TeTeHacko/chytra-budka/firmware/hw/chytra-budka.kicad_sch

## KiCad design firmware/hw/chytra-budka.kicad_sch (2026-08-27)

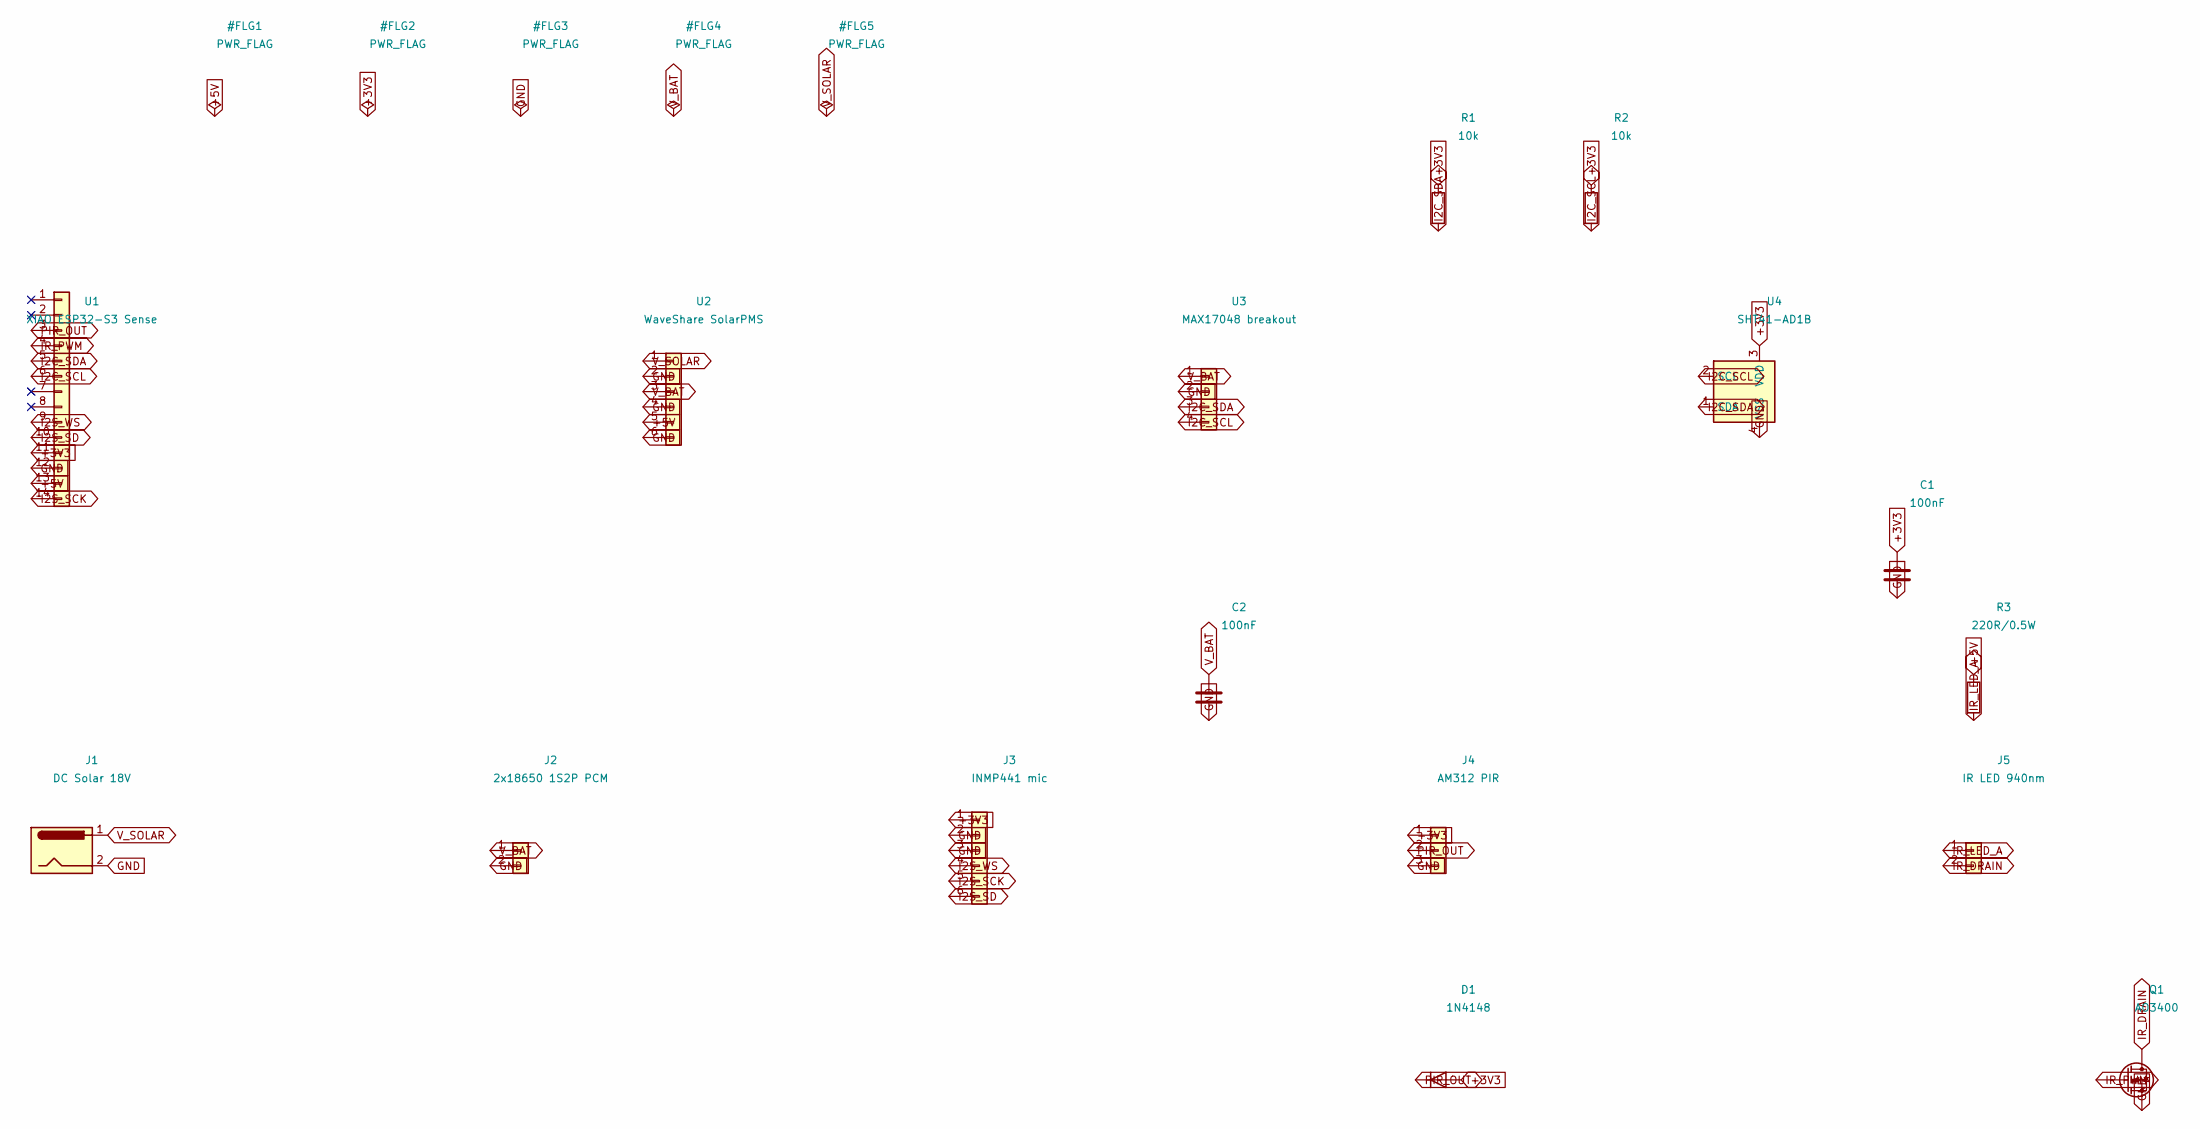
[picture p6: schematic chytra-budka.kicad_sch]

Parts:
C1, C2: 100nF
D1: 1N4148
J1: DC Solar 18V
J2: 2x18650 1S2P PCM
J3: INMP441 mic
J4: AM312 PIR
J5: IR LED 940nm
Q1: AO3400
R1, R2: 10k
R3: 220R/0.5W
U1: XIAO ESP32-S3 Sense
U2: WaveShare SolarPMS
U3: MAX17048 breakout
U4: SHT41-AD1B

Connections:
+3V3: C1.1, D1.2 (A), J3.1, J4.1, R1.1, R2.1, U1.11, U4.3 (VDD)
+5V: R3.1, U1.13, U2.5
GND: C1.2, C2.2, J1.2, J2.2, J3.2, J3.3, J4.3, Q1.S, U1.12, U2.2, U2.4, U2.6, U3.2, U4.4 (VSS)
I2C_SCL: R2.2, U1.6, U3.4, U4.2 (SCL)
I2C_SDA: R1.2, U1.5, U3.3, U4.1 (SDA)
I2S_SCK: J3.5, U1.14
I2S_SD: J3.6, U1.10
I2S_WS: J3.4, U1.9
IR_DRAIN: J5.2, Q1.D
IR_LED_A: J5.1, R3.2
IR_PWM: Q1.G, U1.4
PIR_OUT: D1.1 (K), J4.2, U1.3
V_BAT: C2.1, J2.1, U2.3, U3.1
V_SOLAR: J1.1, U2.1
