TeTeHacko/chytra-budka/firmware/main/http_server.c

/* http_server.c — local HTTP endpoints. See http_server.h. */
#include "http_server.h"

#include "app_config.h"
#include "ble.h"
#include "ble_store.h"
#include "uart_servo.h"

#include <stdio.h>
#include <string.h>

#include <ctype.h>
#include <dirent.h>
#include <errno.h>
#include <fcntl.h>
#include <inttypes.h>
#include <math.h>
#include <stdatomic.h>
#include <stdlib.h>
#include <strings.h>
#include <sys/stat.h>
#include <unistd.h>

#include "app_main_exports.h"
#include "audio.h"
#include "battery.h"
#include "camera.h"
#include "exif_read.h"
#include "config.h"
#include "glitchtip.h"
#include "secrets.h"
#include "secret_helpers.h"
#include "auth_store.h"
#include "tls_enroll.h"
#include "tls_store.h"
#include "wifi_mgr.h"
#include "wifi_store.h"
#include "i18n.h"
#include "sd_layout.h"
#include "ota.h"
#include "esp_system.h"
#include "driver/gpio.h"
#include "device_id.h"
#include "diag.h"
#include "esp_app_desc.h"
#include "esp_heap_caps.h"
#include "freertos/FreeRTOS.h"
#include "freertos/semphr.h"
#include "freertos/task.h"
#include "cb_time.h"
#include "esp_http_server.h"
#include "esp_https_server.h"
#include "esp_log.h"
#include "esp_mac.h"
#include "esp_timer.h"
#include "esp_wifi.h"
#include "mbedtls/base64.h"
#include "i2c_bb.h"
#include "i2c_bus.h"
#include "mqtt.h"
#include "pir.h"
#include "reed.h"
#include "soil.h"
#include "sonar.h"
#include "oled.h"
#include "sd_storage.h"
#include "sensors.h"
#include "text_util.h"
#include "wifi_mgr.h"

static const char *TAG = "http";

/* BLE web-UI helpers shared by root_get (a summary table of connected meters)
 * and the /ble management page, both defined later in this file. */
#define BLE_VIEW_MAX 24
/* Bytes of a JPEG to peek when reading EXIF: the APP1 segment jpeg_stamp.c
 * writes sits right after SOI and is ≤ ~1.1 KB, so 2 KB is ample headroom and
 * avoids copying/parsing the whole (UXGA) frame. */
#define EXIF_PEEK_BYTES 2048

/* Scratch buffer for non-DMA per-request work (EXIF header peeks, SD file
 * reads). Prefer PSRAM so we don't add pressure to the scarce internal DRAM
 * that the BT controller + HW-AES (TLS handshakes) compete for — small plain
 * malloc()s land in internal DRAM (SPIRAM_MALLOC_ALWAYSINTERNAL=4096). Falls
 * back to internal if PSRAM is full. Free with the normal free(). */
static void *scratch_alloc(size_t n) {
    void *p = heap_caps_malloc(n, MALLOC_CAP_SPIRAM);
    return p ? p : malloc(n);
}

static void ble_values_html(const ble_dev_view_t *v, char *out, size_t cap);
static void scan_html_escape(const char *s, char *out, size_t cap);
static void scan_url_decode(const char *s, char *out, size_t cap);

static httpd_handle_t s_server       = NULL;
static httpd_handle_t s_redirect_srv = NULL;
/* True after http_server_start() came up over TLS. HSTS + the Basic
 * auth gate are conditional on this — when the board is in the
 * pre-enrollment HTTP fallback (no cert yet), we don't ship HSTS (it
 * would lock the browser into a non-existent HTTPS) and we don't ask
 * for Basic credentials (the wire is plaintext, so collecting them
 * would be worse than letting LAN users in unauthenticated). */
static bool           s_https_active = false;
/* Cert+key blob outlives the httpd config struct because esp_https_server
 * copies the bytes into its own arena at start (see https_server.c). We
 * still keep the blob alive for the lifetime of the server so a future
 * reload path can re-use it. NULL when running plain HTTP. */
static tls_store_blob_t *s_tls_blob  = NULL;

/* True when HTTP_BASIC_USER/PASS in secrets.h aren't placeholders. The
 * gate also requires s_https_active — basic creds over plaintext is
 * worse than no gate, since the password is recoverable by anybody on
 * the LAN.
 *
 * TODO(fail-closed): when HTTPS is active and placeholders are still
 * in secrets.h, log a loud ESP_LOGW at startup (or refuse to register
 * sensitive handlers). Today a default-config production build serves
 * /mic.wav etc. unauthenticated over HTTPS, which contradicts the
 * "paranoid" deployment posture. Tracked in HTTPS.md follow-ups. */
static bool basic_auth_enabled(void) {
    if (!s_https_active) return false;
    /* Effective creds = operator-set NVS override (via /config or cmd/auth)
     * else the compile-time secrets.h default. */
    char user[AUTH_STORE_USER_CAP], pass[AUTH_STORE_PASS_CAP];
    auth_store_get_effective(user, sizeof(user), pass, sizeof(pass));
    return !secret_is_placeholder(user) && !secret_is_placeholder(pass);
}

/* Set Strict-Transport-Security on HTTPS responses. max-age=15552000 =
 * 180 days; includeSubDomains is safe because *.lan / *.lan aren't
 * also served plain HTTP outside the budka fleet. Skip on plain HTTP
 * (pre-enrollment) so a browser doesn't pin to a non-existent HTTPS
 * endpoint. Idempotent — handlers can call this in addition to
 * basic_auth_gate; the order doesn't matter. */
static void apply_hsts(httpd_req_t *req) {
    if (!s_https_active) return;
    httpd_resp_set_hdr(req, "Strict-Transport-Security",
                       "max-age=15552000; includeSubDomains");
}

/* Check HTTP Basic auth on the incoming request. Returns:
 *   ESP_OK   — gate disabled OR credentials valid
 *   ESP_FAIL — 401 sent; caller must return ESP_OK (NOT ESP_FAIL) so
 *              the httpd loop doesn't log a spurious error
 * Constant-time strcmp not used — the credential is short, the LAN
 * threat model isn't a timing-attack side-channel; if that changes,
 * swap for a CRYPTO_memcmp. */
static esp_err_t basic_auth_gate(httpd_req_t *req) {
    if (!basic_auth_enabled()) return ESP_OK;

    char hdr[256];
    if (httpd_req_get_hdr_value_str(req, "Authorization", hdr, sizeof(hdr)) != ESP_OK) {
        goto deny;
    }
    /* Expect "Basic <base64>" — anything else (Bearer …, Digest …)
     * gets refused with WWW-Authenticate so the client retries with
     * Basic. Case-insensitive scheme per RFC 7235 §2.1. */
    const char *p = hdr;
    if (strncasecmp(p, "Basic ", 6) != 0) goto deny;
    p += 6;
    while (*p == ' ') p++;

    /* Decode base64 → "USER:PASS". 96 bytes covers a 64-char user +
     * 64-char pass + ':' + slack. Anything longer gets rejected. */
    unsigned char dec[96];
    size_t dec_len = 0;
    if (mbedtls_base64_decode(dec, sizeof(dec) - 1, &dec_len,
                              (const unsigned char *)p, strlen(p)) != 0) {
        goto deny;
    }
    dec[dec_len] = 0;
    char *colon = strchr((char *)dec, ':');
    if (!colon) goto deny;
    *colon = 0;
    const char *user = (const char *)dec;
    const char *pass = colon + 1;

    char user_exp[AUTH_STORE_USER_CAP], pass_exp[AUTH_STORE_PASS_CAP];
    auth_store_get_effective(user_exp, sizeof(user_exp), pass_exp, sizeof(pass_exp));
    if (strcmp(user, user_exp) == 0 && strcmp(pass, pass_exp) == 0) {
        return ESP_OK;
    }

deny:
    httpd_resp_set_status(req, "401 Unauthorized");
    /* Realm string just labels the credential prompt in the browser
     * dialog — "chytra-budka" is enough to disambiguate from any other
     * site the LAN user has bookmarks for. */
    httpd_resp_set_hdr(req, "WWW-Authenticate",
                       "Basic realm=\"chytra-budka\", charset=\"UTF-8\"");
    apply_hsts(req);
    httpd_resp_send(req, "auth required\n", HTTPD_RESP_USE_STRLEN);
    return ESP_FAIL;
}

/* One-liner used at the top of sensitive handlers: enforce the gate
 * and apply HSTS in one go. Returns the value the caller should return
 * (ESP_OK to short-circuit on a 401, since the httpd loop interprets
 * ESP_FAIL as "handler failed, drop the socket"). */
#define HTTP_AUTH_OR_RETURN(req) do {                       \
    if (basic_auth_gate((req)) != ESP_OK) return ESP_OK;    \
    apply_hsts((req));                                      \
} while (0)

static void format_mac(char *out, size_t out_sz) {
    uint8_t mac[6] = {0};
    if (esp_read_mac(mac, ESP_MAC_WIFI_STA) != ESP_OK) {
        snprintf(out, out_sz, "??:??:??:??:??:??");
        return;
    }
    snprintf(out, out_sz, "%02x:%02x:%02x:%02x:%02x:%02x", mac[0], mac[1], mac[2], mac[3], mac[4],
             mac[5]);
}

/* Uptime in operator-readable form: "3d 4h 12m", collapsing leading zero
 * units down to "4h 12m" / "12m 5s" / "45s" so a fresh boot reads sanely too.
 * (MQTT/EXIF keep raw seconds for machine parsing; this is for the web UI.) */
static void fmt_uptime(char *out, size_t cap, int64_t secs) {
    if (secs < 0) secs = 0;
    int d = (int)(secs / 86400);
    int h = (int)((secs % 86400) / 3600);
    int m = (int)((secs % 3600) / 60);
    int s = (int)(secs % 60);
    if (d)      snprintf(out, cap, "%dd %dh %dm", d, h, m);
    else if (h) snprintf(out, cap, "%dh %dm", h, m);
    else if (m) snprintf(out, cap, "%dm %ds", m, s);
    else        snprintf(out, cap, "%ds", s);
}

/* Status-row glyphs (shared by the merged Status table): green tick when a
 * subsystem is ready, amber em-dash otherwise. */
#define ST_TICK "&#10003;"
#define ST_DASH "&mdash;"

/* Map a pin-slot function name to a small emoji (HTML entity, so the source
 * stays ASCII) for the homepage pin-map. Icons mirror the HA dashboard's MDI
 * choices (ha/chytra-budka-strategy.js) so the two UIs read the same. Match
 * is substring, ordered most- to least-specific — note pir/i2s are checked
 * before the generic "ir"/"i2c" so they don't get the wrong icon. */
static const char *pin_fn_icon(const char *fn) {
    if (!fn || !strcmp(fn, "none")) return "";
    if (strstr(fn, "pir") || strstr(fn, "motion"))  return "&#128694;&#65039; "; /* 🚶 motion  (HA motion-sensor) */
    if (strstr(fn, "reed") || strstr(fn, "door"))   return "&#128682; ";          /* 🚪 door    (HA door)         */
    if (strstr(fn, "cam"))                          return "&#128247; ";          /* 📷 camera  (HA camera)       */
    if (strstr(fn, "mic") || strstr(fn, "pdm")
        || strstr(fn, "i2s") || strstr(fn, "vad")
        || strstr(fn, "audio"))                     return "&#127897;&#65039; ";  /* 🎙 audio   (HA waveform)     */
    if (strstr(fn, "pcm"))                          return "&#128266; ";          /* 🔊 PCM speaker (PDM 1-bit DAC)*/
    if (strstr(fn, "buzzer"))                       return "&#128276; ";          /* 🔔 buzzer  (LEDC beeper)     */
    if (strstr(fn, "ir"))                           return "&#127769; ";          /* 🌙 IR/night(HA weather-night)*/
    /* "oled" BEFORE "led" — oled_pwr contains the substring "led" and would
     * otherwise grab the LED bulb icon. */
    if (strstr(fn, "oled"))                         return "&#128421;&#65039; ";  /* 🖥 OLED power gate           */
    if (strstr(fn, "led") || strstr(fn, "status"))  return "&#128161; ";          /* 💡 LED     (HA led-on)       */
    if (strstr(fn, "servo"))                        return "&#9881;&#65039; ";    /* ⚙ servo   (HA cog-transfer) */
    if (strstr(fn, "button"))                       return "&#128280; ";          /* 🔘 push-button (cycles OLED) */
    if (strstr(fn, "uart") || strstr(fn, "tx")
        || strstr(fn, "rx"))                        return "&#128268; ";          /* 🔌 serial  (HA serial-port)  */
    if (strstr(fn, "i2c") || strstr(fn, "sda")
        || strstr(fn, "scl"))                       return "&#128279; ";          /* 🔗 I²C bus                   */
    return "&#128205; ";                                                          /* 📍 generic GPIO (HA gpio)    */
}

/* Single source of truth for page styling: a dark, mobile-first theme served
 * once at /style.css and <link>ed from every page (homepage, /config, /wifi,
 * replies). Beats inlining the same CSS into each page — one copy in flash,
 * and the browser caches it across the multi-page session. Mobile: 16px form
 * controls (no iOS focus-zoom), 44px tap targets, full-width fields, fluid
 * layout. Keep the :root palette as the canonical theme. */
static const char STYLE_CSS[] =
    ":root{--bg:#0f1115;--fg:#d4d4d4;--muted:#9aa0a6;--accent:#7fc4ff;"
    "--code-bg:#1a1d23;--row-alt:#161922;--border:#262a33;--field:#161922;"
    "--ok:#3fb950;--warn:#d29922;--ok-bg:#0f2f1a;--ok-fg:#7ee787;"
    "--warn-bg:#2d2607;--warn-fg:#e3b341}"
    "*{box-sizing:border-box}"
    "body{font-family:system-ui,-apple-system,sans-serif;max-width:42em;margin:0 auto;"
    "padding:1em;color:var(--fg);background:var(--bg);line-height:1.5}"
    "a{color:var(--accent);text-decoration:none}a:hover{text-decoration:underline}"
    "h1{margin-bottom:0}h1 small{color:var(--muted);font-size:.6em;font-weight:normal}"
    /* Unified page header (logo + title + cross-page pill nav with an active-
     * page highlight), shared by /, /config and /ble via send_page_head(). */
    "header.hdr{display:flex;align-items:center;gap:.75em;flex-wrap:wrap;"
    "margin:0 0 1.2em;padding:.4em 0 .7em;border-bottom:1px solid var(--border)}"
    ".brand{display:flex;align-items:center;gap:.55em;color:var(--fg);text-decoration:none}"
    ".brand:hover{text-decoration:none}"
    ".logo{width:34px;height:34px;display:block;flex:none}"
    ".btitle{font-size:1.3em;font-weight:600;line-height:1.05}"
    ".btitle small{color:var(--muted);font-size:.62em;font-weight:normal}"
    ".topnav{margin-left:auto;display:flex;gap:.4em;flex-wrap:wrap}"
    ".topnav a{padding:.42em .9em;border:1px solid var(--border);border-radius:999px;"
    "background:var(--code-bg);color:var(--accent);font-size:.95em;font-weight:500}"
    ".topnav a:hover{text-decoration:none;border-color:var(--accent);background:#1f2a37}"
    ".topnav a.cur{background:var(--accent);color:#0b0d12;border-color:var(--accent)}"
    "@media(max-width:30em){.topnav{width:100%;margin-left:0}.topnav a{flex:1;text-align:center}}"
    "h2{margin-top:1.5em;border-bottom:1px solid var(--border);padding-bottom:.2em}"
    "h3{margin-top:1.3em;border-bottom:1px solid var(--border);padding-bottom:.2em}"
    "code{background:var(--code-bg);padding:.1em .3em;border-radius:3px}"
    "label{display:block;margin:.35em 0}"
    "input,select{width:100%;font-size:16px;padding:.55em;margin-top:.25em;color:var(--fg);"
    "background:var(--field);border:1px solid var(--border);border-radius:8px}"
    "button{font-size:16px;padding:.6em 1em;margin:.2em 0;background:#1f2a37;color:var(--fg);"
    "border:1px solid var(--border);border-radius:8px;cursor:pointer;min-height:44px}"
    "button:hover{background:#2a3441}"
    "small{color:var(--muted)}"
    "details{border:1px solid var(--border);border-radius:8px;margin:.4em 0;padding:0 .7em}"
    "summary{cursor:pointer;padding:.6em 0;font-weight:bold}"
    "details[open]{padding-bottom:.4em}"
    /* Security warning strips: red, one per line (each is its own block div),
     * spaced so stacked warnings read as a list. */
    ".warn-bar{background:#7f1d1d;color:#fee2e2;border:1px solid #ef4444;"
    "border-radius:8px;padding:.6em .8em;margin:0 0 .5em;font-size:.95em}"
    ".warn-bar a{color:#fff;text-decoration:underline;display:block}"
    /* WiFi scan picker list — finger-friendly: tall, well-spaced tap-card rows
     * with a big bold SSID. Don't crowd them; this is tapped on a phone during
     * onboarding where mis-taps mean retyping. */
    "ul.scan{list-style:none;padding:0;margin:.6em 0}"
    "ul.scan li{margin:.5em 0}"
    "ul.scan a{display:flex;gap:.7em;align-items:center;padding:.9em 1em;min-height:60px;"
    "background:#1f2a37;border:1px solid var(--border);border-radius:10px;color:var(--fg);"
    "font-size:1.1em}"
    "ul.scan a:hover{text-decoration:none;border-color:var(--accent)}"
    "ul.scan a:active{background:#2a3441;border-color:var(--accent)}"
    ".bars{font-family:monospace;letter-spacing:1px;color:var(--accent)}"
    ".ssid{flex:1;font-weight:600;overflow:hidden;text-overflow:ellipsis;white-space:nowrap}"
    ".dbm{opacity:.6;font-size:.8em;white-space:nowrap}"
    ".micgain{margin:.5em 0;display:flex;align-items:center;gap:.5em;flex-wrap:wrap}"
    ".micgain input[type=range]{flex:1;min-width:140px}"
    "table{border-collapse:collapse;width:100%}"
    "td{padding:.25em .6em;vertical-align:top}"
    "td.k{color:var(--muted);width:11em}td.v{font-variant-numeric:tabular-nums}"
    "td.ok{color:var(--ok);width:1.5em;text-align:center;font-weight:bold}"
    "td.warn{color:var(--warn);width:1.5em;text-align:center;font-weight:bold}"
    "tr:nth-child(even){background:var(--row-alt)}"
    "td.size{color:var(--muted);text-align:right;white-space:nowrap}"
    "td.tag{color:var(--muted);font-size:.85em}"
    ".empty{color:var(--muted);padding:1em 0}"
    ".summary{padding:.4em .8em;border-radius:4px;display:inline-block;margin-left:.5em;font-size:.8em}"
    ".s-ok{background:var(--ok-bg);color:var(--ok-fg)}"
    ".s-degraded{background:var(--warn-bg);color:var(--warn-fg)}"
    "audio{width:100%;margin-top:.5em;filter:invert(.9) hue-rotate(180deg)}"
    ".actions{display:flex;gap:.6em;margin:.8em 0;flex-wrap:wrap}"
    /* Action controls are <a> links (work without JS — JS just enhances them
     * into in-page capture/stream); style them identically to buttons. */
    ".actions a,.actions button{flex:1;font-size:1.15em;padding:.7em .5em;min-height:3em;"
    "background:#1f2a37;color:var(--fg);border:1px solid var(--border);border-radius:8px;"
    "cursor:pointer;display:flex;align-items:center;justify-content:center;text-decoration:none}"
    ".actions a:hover{text-decoration:none}"
    /* Photo frame: positioned wrapper that RESERVES the capture aspect-ratio
     * (set inline from the camera framesize — no hardcoded ratio) so the preview
     * doesn't reflow when /last.jpg loads or 404s. A placeholder (.ph) sits
     * behind the image and shows when there's no frame; the caption (.cap)
     * overlays bottom-left (HTML/CSS only, no pixel burn-in — see jpeg_stamp.h). */
    ".frame{position:relative;display:block;width:100%;max-width:100%;margin:.5em 0;"
    "border-radius:4px;overflow:hidden;background:var(--code-bg)}"
    ".frame img{position:relative;z-index:1;display:block;width:100%;height:100%;"
    "object-fit:contain;border-radius:4px}"
    /* Placeholder sits BEHIND the image (z-index 0 vs img's 1) — a positioned
     * .ph would otherwise paint OVER the static img. JS also hides it on load so
     * it never shows through a stream's letterbox bars. */
    ".frame .ph{position:absolute;inset:0;z-index:0;display:flex;align-items:center;"
    "justify-content:center;color:var(--muted);font-size:.95em}"
    /* Caption above the image (z 2 > img 1 > placeholder 0). */
    ".frame .cap{position:absolute;left:0;bottom:0;z-index:2;max-width:100%;margin:0;"
    "background:rgba(0,0,0,.6);color:#fff;padding:.3em .55em;font-size:.8em;"
    "line-height:1.3;border-radius:0 6px 0 4px;font-variant-numeric:tabular-nums}"
    "@media(max-width:48em){td.k{width:auto}table{font-size:.95em}}";

/* GET /style.css — the shared theme. No auth (it's just styling, requested
 * before any login) and cached so it isn't refetched on every page. */
static esp_err_t style_css_get(httpd_req_t *req) {
    httpd_resp_set_type(req, "text/css");
    httpd_resp_set_hdr(req, "Cache-Control", "max-age=86400");
    return httpd_resp_send(req, STYLE_CSS, HTTPD_RESP_USE_STRLEN);
}

/* Embedded brand assets (see CMakeLists.txt EMBED_*). favicon.ico is binary
 * (start/end bound the length); logo.svg rides EMBED_TXTFILES so it's
 * NUL-terminated and serves with HTTPD_RESP_USE_STRLEN. */
extern const uint8_t favicon_ico_start[] asm("_binary_favicon_ico_start");
extern const uint8_t favicon_ico_end[] asm("_binary_favicon_ico_end");
extern const char logo_svg_start[] asm("_binary_logo_svg_start");

/* GET /favicon.ico — the embedded site icon. No auth (browsers fetch it before
 * any login); cached a week so it isn't re-requested. */
static esp_err_t favicon_get(httpd_req_t *req) {
    httpd_resp_set_type(req, "image/x-icon");
    httpd_resp_set_hdr(req, "Cache-Control", "max-age=604800");
    return httpd_resp_send(req, (const char *)favicon_ico_start,
                           (ssize_t)(favicon_ico_end - favicon_ico_start));
}

/* GET /logo.svg — the monochrome mark shown in every page's header. No auth,
 * cached a week (the <header> links it from /, /config and /ble). */
static esp_err_t logo_svg_get(httpd_req_t *req) {
    httpd_resp_set_type(req, "image/svg+xml");
    httpd_resp_set_hdr(req, "Cache-Control", "max-age=604800");
    return httpd_resp_send(req, logo_svg_start, HTTPD_RESP_USE_STRLEN);
}

/* Persistent top warning bar for insecure DEFAULTS, emitted on every page so
 * the operator can't miss it. Fires when (a) the recovery AP is up on its
 * public default password, and/or (b) web-admin basic-auth is a placeholder
 * (gate off) or the example default we ship. Emits nothing when both are fine.
 * Uses chunked send (works mid-stream on all the page handlers). */
static void send_security_banner(httpd_req_t *req) {
    char aps[WIFI_STORE_SSID_CAP], app[WIFI_STORE_PASS_CAP];
    bool ap_custom = false;
    wifi_store_get_ap(aps, sizeof(aps), app, sizeof(app), &ap_custom);
    bool ap_default = (wifi_mgr_softap_active() || wifi_store_is_ap_only()) && !ap_custom;
    /* Weak web-admin auth: gate effectively off (placeholder creds / no HTTPS)
     * OR still on the public example default. Uses the EFFECTIVE pass so the
     * banner clears once the operator sets a real password via /config or
     * cmd/auth. */
    char eff_u[AUTH_STORE_USER_CAP], eff_p[AUTH_STORE_PASS_CAP];
    auth_store_get_effective(eff_u, sizeof(eff_u), eff_p, sizeof(eff_p));
    /* "cb" is the easy out-of-box default (secrets.h) — flag it as weak so the
     * banner nags until the operator sets a real login. */
    bool auth_weak = !basic_auth_enabled() || strcmp(eff_p, "cb") == 0;
    if (!ap_default && !auth_weak) return;
    /* One red strip PER warning (each its own block div → own line), and each
     * is a link straight to the /config section that fixes it (#ap / #auth —
     * the anchors on those section headings). */
    char bar[512];
    if (ap_default) {
        snprintf(bar, sizeof(bar),
                 "<div class=\"warn-bar\"><a href=\"/config#ap\">&#9888; %s</a></div>",
                 tr(STR_WARN_AP_DEFAULT));
        httpd_resp_sendstr_chunk(req, bar);
    }
    if (auth_weak) {
        snprintf(bar, sizeof(bar),
                 "<div class=\"warn-bar\"><a href=\"/config#auth\">&#9888; %s</a></div>",
                 tr(STR_WARN_AUTH_DEFAULT));
        httpd_resp_sendstr_chunk(req, bar);
    }
}

/* Forward decls — definitions live with the WiFi-scan helpers further down. */
static void scan_html_escape(const char *s, char *out, size_t cap);
static const char *rssi_bars(int rssi);  /* RSSI → 4-cell █/░ signal bar */

/* Shared page chrome for every page (/, /config, /ble) so they read
 * identically: the <head> (+ optional extra head markup, e.g. the BLE
 * auto-refresh meta), opening <body>, the security banner, and a header bar
 * carrying the embedded logo, the title and the cross-page nav. Each page then
 * emits only its own sections. Replaces the per-page ad-hoc <h1>/<h2> + Home
 * link that had drifted apart across the three pages. */
static void send_page_head(httpd_req_t *req, const char *head_extra,
                           const char *active) {
    httpd_resp_set_type(req, "text/html; charset=utf-8");
    /* Version-stamp the /style.css + /logo.svg URLs so a firmware update busts
     * the browser cache (they're served with a long max-age; without this an
     * old cached stylesheet renders the new markup unstyled). */
    const char *ver = esp_app_get_description()->version;
    char buf[768];
    int n = snprintf(buf, sizeof(buf),
        "<!doctype html><html><head><meta charset=\"utf-8\">"
        "<meta name=\"viewport\" content=\"width=device-width, initial-scale=1\">"
        "<title>Chytrá Budka %s</title>"
        "<meta name=\"color-scheme\" content=\"dark\">"
        "<link rel=\"icon\" href=\"/favicon.ico\">"
        "<link rel=\"stylesheet\" href=\"/style.css?v=%s\">%s"
        "</head><body>",
        device_id_suffix(), ver, head_extra ? head_extra : "");
    httpd_resp_send_chunk(req, buf, n);
    send_security_banner(req);
    /* Mark the current page's nav pill so it reads as "you are here". */
    const char *cur_home = (active && !strcmp(active, "home")) ? "cur" : "";
    const char *cur_cfg  = (active && !strcmp(active, "config")) ? "cur" : "";
    const char *cur_ble  = (active && !strcmp(active, "ble")) ? "cur" : "";
    n = snprintf(buf, sizeof(buf),
        "<header class=\"hdr\">"
        "<a class=\"brand\" href=\"/\">"
        "<img class=\"logo\" src=\"/logo.svg?v=%s\" alt=\"\" width=\"34\" height=\"34\">"
        "<span class=\"btitle\">Chytrá Budka <small>%s</small></span></a>"
        "<nav class=\"topnav\">"
        "<a class=\"%s\" href=\"/\">%s</a>"
        "<a class=\"%s\" href=\"/config\">%s</a>"
        "<a class=\"%s\" href=\"/ble\">BLE</a>"
        "</nav></header>",
        ver, device_id_suffix(),
        cur_home, tr(STR_NAV_HOME), cur_cfg, tr(STR_SETTINGS), cur_ble);
    httpd_resp_send_chunk(req, buf, n);
}

/* "YYYY:MM:DD HH:MM:SS" → "YYYY-MM-DD HH:MM:SS" (EXIF date uses colons). */
static void exif_reformat_dt(const char *in, char *out, size_t cap) {
    snprintf(out, cap, "%s", in ? in : "");
    if (strlen(out) >= 10) {
        if (out[4] == ':') out[4] = '-';
        if (out[7] == ':') out[7] = '-';
    }
}

/* Compact one-line overlay caption built from a photo's EXIF: capture time,
 * trigger, and a battery (or RSSI) hint. The trigger is HTML-escaped (EXIF is
 * untrusted SD content); the rest are digits/symbols. &nbsp; keeps a value
 * glued to its unit. `out` is empty if there's nothing worth showing. */
static void exif_caption_html(const exif_meta_t *m, char *out, size_t cap) {
    if (cap == 0) return;
    out[0] = 0;
    char dt[24];
    if (m->have_dt) exif_reformat_dt(m->datetime, dt, sizeof(dt));
    else            snprintf(dt, sizeof(dt), "%s", tr(STR_NO_CLOCK));
    int o = snprintf(out, cap, "%s", dt);
    if (o < 0) { out[0] = 0; return; }

    if (m->trigger[0] && (size_t)o < cap) {
        char te[40];
        scan_html_escape(m->trigger, te, sizeof(te));
        o += snprintf(out + o, cap - (size_t)o, " &middot; %.39s", te);
    }
    double vb, soc, rssi;
    if ((size_t)o < cap && exif_json_num(m->user_json, "vbatt", &vb)) {
        if (exif_json_num(m->user_json, "soc", &soc))
            o += snprintf(out + o, cap - (size_t)o,
                          " &middot; %.2f&nbsp;V (%.0f&nbsp;%%)", vb, soc);
        else
            o += snprintf(out + o, cap - (size_t)o, " &middot; %.2f&nbsp;V", vb);
    } else if ((size_t)o < cap && exif_json_num(m->user_json, "rssi", &rssi)) {
        o += snprintf(out + o, cap - (size_t)o, " &middot; %.0f&nbsp;dBm", rssi);
    }
    /* Ambient temperature · humidity (SHT41) · pressure (BMP388) · camera AGC —
     * all from the UserComment telemetry, each shown only when present. */
    double tC, rh, pa, agc;
    if ((size_t)o < cap && exif_json_num(m->user_json, "temp", &tC))
        o += snprintf(out + o, cap - (size_t)o, " &middot; %.1f&nbsp;&deg;C", tC);
    if ((size_t)o < cap && exif_json_num(m->user_json, "humidity", &rh))
        o += snprintf(out + o, cap - (size_t)o, " &middot; %.0f&nbsp;%%", rh);
    if ((size_t)o < cap && exif_json_num(m->user_json, "pressure", &pa))
        o += snprintf(out + o, cap - (size_t)o, " &middot; %.0f&nbsp;hPa", pa);
    if ((size_t)o < cap && exif_json_num(m->user_json, "agc", &agc))
        o += snprintf(out + o, cap - (size_t)o, " &middot; AGC&nbsp;%.0f", agc);
}

static esp_err_t root_get(httpd_req_t *req) {
    apply_hsts(req);
    char mac[20];
    format_mac(mac, sizeof(mac));
    const esp_app_desc_t *app = esp_app_get_description();
    int64_t uptime_s = esp_timer_get_time() / 1000000;

    /* SHT41 readings — use the cached value from the most recent
     * telemetry tick instead of triggering a fresh 12 ms blocking I²C
     * read on every page load. Telemetry refreshes the cache once per
     * mode-dependent period (60s in Continuous, 300s in Triggered) so
     * the value here is at most that stale, which is acceptable for an
     * info page and avoids contention with the camera SCCB on I²C0. */
    /* Physical I²C sensor values are rendered below straight from the
     * sensor registry's caches (populated by the telemetry tick) — the
     * HTTP task does NO live I²C read, which avoids adding a concurrent
     * caller on the shared bus (the source of the OLED flush timeouts).
     * Battery (MAX17048) is one of those registry sensors now, so it's
     * rendered in the loop below too — no separate battery row. */

    int rssi = 0;
    wifi_ap_record_t ap;
    if (esp_wifi_sta_get_ap_info(&ap) == ESP_OK)
        rssi = ap.rssi;

    uint32_t pir_count = pir_motion_count();
    uint32_t audio_bursts = audio_burst_count();
    uint32_t photo_count = camera_capture_count();
    uint32_t heap_free = esp_get_free_heap_size();

    uint64_t sd_free = 0, sd_total = 0;
    sd_storage_stats(&sd_free, &sd_total);

    /* Status rows — the connected sensors (SHT/BMP/battery/solar) render from
     * the CB_SENSORS registry loop below, so no per-sensor bool is needed here;
     * only the always-shown subsystems + the armed-only PIR/reed keep a flag. */
    bool b_sd = sd_storage_ready();
    bool b_cam = camera_ready();
    bool b_pir = pir_ready();
    bool b_reed = reed_ready();
    bool b_mic = audio_ready();
    bool b_audio_task = audio_task_running();
    bool b_cam_worker = camera_worker_running();
    bool b_wifi = wifi_mgr_is_connected();
    bool b_mqtt = mqtt_is_connected();
    /* In full AP-only mode there is no station by design, so STA/MQTT being
     * "down" is the expected state, not a fault. */
    bool b_ap = wifi_store_is_ap_only();

    /* Page exceeds a single 4 KB block, so build it incrementally with
     * httpd_resp_send_chunk(). Each chunk gets its own bounded buffer
     * so a snprintf overflow corrupts at most that chunk, never the
     * whole response.
     *
     * Buffer is heap-allocated rather than on stack — keeps 1 KB out of
     * the handler's stack frame while sht41_read / esp_wifi_sta_get_ap_info
     * / battery_* go deep on the same stack. */
#define CHUNK_SZ 1024
    char *chunk = (char *)malloc(CHUNK_SZ);
    if (!chunk) {
        httpd_resp_send_err(req, HTTPD_500_INTERNAL_SERVER_ERROR, "OOM allocating response buffer");
        return ESP_FAIL;
    }
    httpd_resp_set_type(req, "text/html; charset=utf-8");

/* snprintf returns the would-be length; if a chunk's format expands past
 * CHUNK_SZ it does NOT overflow the buffer, but passing that oversized count
 * to httpd_resp_send_chunk would read PAST the buffer (heap over-read leaking
 * adjacent memory into the response). Clamp to what actually fits and shout
 * in the log so an over-long chunk is caught in dev rather than shipped. */
#define SEND(fmt, ...)                                          \
    do {                                                        \
        int _n = snprintf(chunk, CHUNK_SZ, fmt, ##__VA_ARGS__); \
        if (_n >= CHUNK_SZ) {                                   \
            ESP_LOGW(TAG, "SEND chunk truncated (%d >= %d) — split the literal", \
                     _n, CHUNK_SZ);                             \
            _n = CHUNK_SZ - 1;                                  \
        }                                                       \
        if (_n > 0)                                             \
            httpd_resp_send_chunk(req, chunk, _n);              \
    } while (0)

    send_page_head(req, NULL, "home");

    /* Top action bar — Capture + Stream are the two controls used most when
     * physically positioning the box, so they sit at the very top with big
     * touch targets and a shared preview area right below. /capture triggers a
     * fresh shot and returns it; /stream.mjpg is the live MJPEG view. The
     * cache-buster on /capture forces the browser to re-fetch on every tap.
     * The preview defaults to the last stored frame (/last.jpg) so you see the
     * current framing immediately on load; onerror hides it if no shot yet. */
    /* Reserve the preview box at the camera's CAPTURE aspect-ratio (read from
     * cam_framesize — never hardcoded) so the layout doesn't jump when /last.jpg
     * loads or 404s; a placeholder shows until/unless there's a frame. */
    uint16_t cam_w = 0, cam_h = 0;
    char framestyle[40] = "";
    if (camera_capture_dimensions(&cam_w, &cam_h))
        snprintf(framestyle, sizeof(framestyle), " style=\"aspect-ratio:%u/%u\"",
                 (unsigned)cam_w, (unsigned)cam_h);
    /* Deep-link the static preview to the stored photo's viewer (server-side,
     * no JS) when there's a last-saved frame. The /view param charset is the
     * same alnum + . _ - the filename uses and the bucket is
     * "YYYY-MM-DD"/"boot"/"root", so no escaping is needed. The <a> wraps only
     * the <img>; JS shoot()/stream() still swaps the inner src in place. */
    char view_open[128] = "";
    const char *view_close = "";
    {
        char ld[SD_LAYOUT_DAY_LEN], lf[SD_LAYOUT_LEAF_MAX];
        if (sd_storage_last_photo(ld, sizeof(ld), lf, sizeof(lf))) {
            snprintf(view_open, sizeof(view_open),
                     "<a id=\"viewlink\" href=\"/view?d=%s&amp;f=%s\">", ld, lf);
            view_close = "</a>";
        }
    }
    SEND(
        /* Real <a> links so the page is usable with JavaScript OFF: Capture
         * opens a fresh JPEG, Stream opens the MJPEG. With JS, shoot()/stream()
         * intercept the click (return false) and swap the image in-page instead
         * of navigating. Settings/BLE navigation lives in the header nav now, so
         * the action bar is just the two capture controls. */
        "<div class=\"actions\">"
        "<a id=\"btn-cap\" href=\"/capture\" onclick=\"return shoot()\">&#128247; %s</a>"
        "<a id=\"btn-str\" href=\"/stream.mjpg\" onclick=\"return stream()\">&#127909; %s</a>"
        "</div>"
        "<div class=\"frame\"%s>"
        "<div class=\"ph\">&#128247; %s</div>"
        "%s<img id=\"view\" alt=\"\" src=\"/last.jpg\" "
        "onerror=\"this.style.display='none'\">%s",
        tr(STR_HP_CAPTURE), tr(STR_HP_STREAM),
        framestyle, tr(STR_HP_NOPHOTO), view_open, view_close);
    /* Overlay the last stored frame's capture time + telemetry, read straight
     * from its EXIF (peek the JPEG header only — no full decode). JS swaps the
     * <img> to a live capture/stream on tap and hides this caption (it would be
     * stale against the new frame); the static last-frame view keeps it. */
    {
        uint8_t *hdrbuf = (uint8_t *)scratch_alloc(EXIF_PEEK_BYTES);
        if (hdrbuf) {
            size_t hn = camera_last_jpeg_peek_header(hdrbuf, EXIF_PEEK_BYTES);
            exif_meta_t lm;
            if (hn && exif_read(hdrbuf, hn, &lm)) {
                char capt[256];
                exif_caption_html(&lm, capt, sizeof(capt));
                if (capt[0]) SEND("<div class=\"cap\" id=\"cap\">%s</div>", capt);
            }
            free(hdrbuf);
        }
    }
    SEND("</div>");  /* close .frame */
    /* Live mic right under the photo/stream preview (its natural home — the
     * other "live view" of the box), not buried at the bottom by the
     * endpoints list. */
    /* Live mic + browser-side gain — only when the mic is actually capturing
     * (audio_ready() = i2s channel up AND ≥1 frame read). When the PDM mic is
     * absent / disconnected (no DMA data) there's nothing to stream, so hide
     * the player entirely rather than offer a dead control. The ESP serves the
     * raw PDM WAV at unity (no on-device boost), which is very quiet; route the
     * <audio> through a Web Audio GainNode so a slider can amplify it up to 10x
     * in the browser. No-JS fallback: the <audio controls> still plays at 1x. */
    if (audio_ready()) {
        /* Gain integrated INTO the player: no separate slider. The PDM mic is
         * quiet, so route playback through a fixed 10x Web-Audio boost and let
         * the <audio> element's own volume control set the effective gain — the
         * element's volume (0-1) scales the source ahead of the 10x node, so the
         * player's volume slider spans 0-10x. Default 0.3 ~ 3x (the old default). */
        SEND("<h3>%s</h3>"
             "<audio id=\"mic\" controls preload=\"none\" src=\"/mic.wav\"></audio>"
             "<script>"
             "(function(){var a=document.getElementById('mic'),"
             "AC=window.AudioContext||window.webkitAudioContext;if(!a||!AC)return;"
             "a.volume=0.3;var c,g;"
             "a.addEventListener('play',function(){if(!c){c=new AC();"
             "var sr=c.createMediaElementSource(a);g=c.createGain();g.gain.value=10;"
             "sr.connect(g);g.connect(c.destination);}"
             "if(c.state=='suspended')c.resume();});})();"
             "</script>",
             tr(STR_H_LIVEMIC));
    }
    /* Capture/stream toggle. Capture swaps in a fresh /capture JPEG and, once it
     * loads, re-shows the caption with THAT frame's EXIF (via showCap()/last.json
     * — capture refreshes the last-frame cache). Stream points the <img> at the
     * live MJPEG and hides the caption (live frames have no single timestamp);
     * Stop reloads the latest stored frame (/last.jpg) + its caption rather than
     * clearing the preview. Helpers split across two <script>s (shared globals)
     * to keep each chunk under the SEND buffer. */
    SEND(
        "<script>"
        "var v=document.getElementById('view'),"
        "sb=document.getElementById('btn-str'),st=false;"
        /* Show the placeholder ONLY when no frame is displayed: hide it once the
         * <img> loads (covers the stream-letterbox case too), show it on error. */
        "var ph=v?v.parentNode.querySelector('.ph'):null;"
        "function setPh(s){if(ph)ph.style.display=s?'':'none';}"
        "if(v){v.addEventListener('load',function(){setPh(0);});"
        "v.addEventListener('error',function(){setPh(1);});"
        "if(v.complete&&v.naturalHeight>0)setPh(0);}"
        "function hc(){var c=document.getElementById('cap');if(c)c.style.display='none';}"
        "</script>");
    SEND(
        "<script>"
        "function fmtCap(j){if(!j||j.exif!==true)return '';"
        "var dt=(j.have_dt===false)?'':(j.datetime||'').replace(/^(\\d{4}):(\\d{2}):/,'$1-$2-');"
        "var p=[];if(dt)p.push(dt);if(j.trigger)p.push(j.trigger);"
        "var t=j.telemetry||{};"
        "if(typeof t.vbatt==='number'){var b=t.vbatt.toFixed(2)+'\\u00a0V';"
        "if(typeof t.soc==='number')b+=' ('+Math.round(t.soc)+'\\u00a0%%)';p.push(b);}"
        "else if(typeof t.rssi==='number')p.push(Math.round(t.rssi)+'\\u00a0dBm');"
        "if(typeof t.temp==='number')p.push(t.temp.toFixed(1)+'\\u00a0\\u00b0C');"
        "if(typeof t.humidity==='number')p.push(Math.round(t.humidity)+'\\u00a0%%');"
        "if(typeof t.pressure==='number')p.push(Math.round(t.pressure)+'\\u00a0hPa');"
        "if(typeof t.agc==='number')p.push('AGC\\u00a0'+t.agc);"
        "return p.join(' \\u00b7 ');}"
        "</script>");
    SEND(
        "<script>"
        "function showCap(){fetch('/last.json').then(function(r){return r.json();})"
        ".then(function(j){var x=fmtCap(j);if(!x)return;"
        "var c=document.getElementById('cap');"
        "if(!c){c=document.createElement('div');c.id='cap';c.className='cap';"
        "if(v.parentNode)v.parentNode.appendChild(c);}"
        "c.textContent=x;c.style.display='';}).catch(function(){});}"
        "</script>");
    SEND(
        "<script>"
        "function rst(){st=false;sb.innerHTML='&#127909; %s';}"
        "function shoot(){if(st)rst();v.style.display='block';hc();setPh(0);"
        "v.onload=function(){v.onload=null;showCap();};"
        "v.src='/capture?t='+Date.now();return false;}"
        "function stream(){if(st){v.onload=function(){v.onload=null;showCap();};"
        "v.style.display='block';v.src='/last.jpg?t='+Date.now();rst();}"
        "else{v.onload=null;v.style.display='block';hc();setPh(0);v.src='/stream.mjpg';st=true;"
        "sb.innerHTML='&#9209; %s';}return false;}"
        "</script>",
        tr(STR_HP_STREAM), tr(STR_HP_STOP));

    /* ── Status — one operator-facing table merging the old "Self-test" and
     * "Live sensors": the core subsystems every board has (always shown, ✓ or
     * —), then connected peripherals/sensors with their live reading folded in
     * (absent ones emit no row), then operator counters. Debug internals (tasks,
     * heap, stack, DMA) drop into the collapsed Diagnostics block below. No
     * N/N summary badge — optional sensors are normally absent, so it would
     * permanently read "degraded — some sensors not wired" and mean nothing;
     * the truthful per-check verdict lives in /selftest for a deeper look. */
    SEND("<h2>%s</h2><table>", tr(STR_H_STATUS));

    /* WiFi: the same signal bar + thresholds as the scan list, then RSSI and
     * the joined SSID/BSSID (so the operator sees exactly what it joined). */
    if (b_ap) {
        SEND("<tr><td class=\"ok\">" ST_TICK "</td><td>WiFi</td><td>%s</td></tr>",
             tr(STR_ST_AP_MODE));
    } else if (b_wifi) {
        char esc_ssid[200], bssid[18] = {0};
        scan_html_escape(wifi_mgr_get_ssid(), esc_ssid, sizeof(esc_ssid));
        wifi_mgr_get_bssid(bssid, sizeof(bssid));
        SEND("<tr><td class=\"ok\">" ST_TICK "</td><td>WiFi</td>"
             "<td><span class=\"bars\">%s</span> %d&nbsp;dBm &middot; %s (%s)</td></tr>",
             rssi_bars(rssi), rssi, esc_ssid, bssid[0] ? bssid : "?");
    } else {
        SEND("<tr><td class=\"warn\">" ST_DASH "</td><td>WiFi</td><td>%s</td></tr>",
             tr(STR_ST_NO_ASSOC));
    }
    SEND("<tr><td class=\"%s\">%s</td><td>MQTT</td><td>%s</td></tr>",
         (b_ap || b_mqtt) ? "ok" : "warn", (b_ap || b_mqtt) ? ST_TICK : ST_DASH,
         b_ap ? tr(STR_ST_NA_AP) : b_mqtt ? tr(STR_ST_BROKER_OK) : tr(STR_ST_DISCONNECTED));
    SEND("<tr><td class=\"%s\">%s</td><td>%s</td><td>%s</td></tr>",
         b_cam ? "ok" : "warn", b_cam ? ST_TICK : ST_DASH,
         tr(STR_LBL_CAMERA), b_cam ? tr(STR_ST_READY) : tr(STR_D_SCCB));
    SEND("<tr><td class=\"%s\">%s</td><td>%s</td><td>%s</td></tr>",
         b_mic ? "ok" : "warn", b_mic ? ST_TICK : ST_DASH,
         tr(STR_LBL_MIC), b_mic ? tr(STR_D_MIC_OK) : tr(STR_D_MIC_NO));
    /* (audio_task / cam_worker — the pinned CPU1 tasks — are internals, so they
     * live in the Diagnostics block below, not in the operator Status.) */

    /* microSD: usage bar when mounted (red >90 %, amber >75 %), else "—". */
    if (b_sd && sd_total > 0) {
        uint64_t used = sd_total - sd_free;
        unsigned pct = (unsigned)((used * 100ULL) / sd_total);
        const char *color = (pct >= 90) ? "#cf222e" : (pct >= 75) ? "#bf8700" : "#1a7f37";
        SEND(
            "<tr><td class=\"ok\">" ST_TICK "</td><td>microSD</td><td>"
            "<div style=\"display:flex;align-items:center;gap:0.6em\">"
            "<div style=\"flex:1;height:0.8em;background:#30363d;border-radius:3px;overflow:hidden\">"
            "<div style=\"width:%u%%;height:100%%;background:%s\"></div></div>"
            "<span>%u%% &mdash; %llu / %llu MB %s</span></div></td></tr>",
            pct, color, pct, sd_free / (1024ULL * 1024ULL),
            sd_total / (1024ULL * 1024ULL), tr(STR_S_FREE));
    } else {
        SEND("<tr><td class=\"warn\">" ST_DASH "</td><td>microSD</td><td>%s</td></tr>",
             tr(STR_D_NOT_MOUNTED));
    }

    /* Connected I²C sensors from the registry — one ✓ row each (name + joined
     * channel readings), present-only (absent sensors read nothing → no row).
     * Covers both SHT41s, BMP388, MAX17048 and INA226 on each bus; adding a
     * sensor here makes it appear automatically. Readings come from the
     * telemetry-refreshed caches (no live I²C from the HTTP task). */
    for (size_t si = 0; si < CB_SENSORS_N; si++) {
        const cb_sensor_t *sen = &CB_SENSORS[si];
        char vals[160];
        int o = 0;
        for (size_t ci = 0; ci < sen->n_chans; ci++) {
            const cb_chan_t *c = &sen->chans[ci];
            float v;
            if (c->read(&v) && isfinite(v))
                o += snprintf(vals + o, sizeof(vals) - o, "%s%.*f %s",
                              o ? " &middot; " : "", c->decimals, v, c->unit);
        }
        if (o == 0)
            continue;  /* sensor absent / not reading → no row */
        SEND("<tr><td class=\"ok\">" ST_TICK "</td><td>%s</td><td>%s</td></tr>",
             sen->name, vals);
    }
    /* MCU die temperature — a genuine sensor reading (not a debug internal), so
     * it sits with the other sensors rather than in Diagnostics. */
    {
        float mcu_c = diag_mcu_temp_c();
        if (isfinite(mcu_c))
            SEND("<tr><td class=\"ok\">" ST_TICK "</td><td>%s</td>"
                 "<td>%.1f &deg;C</td></tr>", tr(STR_S_MCU_TEMP), mcu_c);
    }

    /* PIR / reed — peripherals that may be absent, so shown only when armed
     * (a stock board carries no permanent "—" for them). */
    if (b_pir) {
        char pir_armed[56];
        snprintf(pir_armed, sizeof(pir_armed), tr(STR_D_PIR_ARMED_FMT),
                 app_config_pin_for_first("pir"));
        SEND("<tr><td class=\"ok\">" ST_TICK "</td><td>PIR</td><td>%s</td></tr>",
             pir_armed);
    }
    if (b_reed) {
        SEND("<tr><td class=\"ok\">" ST_TICK "</td><td>%s</td>"
             "<td>%s &middot; %" PRIu32 " %s</td></tr>",
             tr(STR_LBL_REED), reed_is_closed() ? tr(STR_ST_CLOSED) : tr(STR_ST_OPEN),
             reed_event_count(), tr(STR_S_EVENTS));
    }
    /* Grove sensors — same only-when-armed policy as PIR/reed. Values
     * come from the modules' caches (sonar poll task / telemetry-tick
     * soil read); "—" = armed but no valid reading yet. */
    if (sonar_ready()) {
        float cm;
        if (sonar_last_cm(&cm))
            SEND("<tr><td class=\"ok\">" ST_TICK "</td><td>%s</td>"
                 "<td>%.1f cm</td></tr>", tr(STR_LBL_SONAR), cm);
        else if (sonar_is_clear())
            SEND("<tr><td class=\"ok\">" ST_TICK "</td><td>%s</td>"
                 "<td>&infin;</td></tr>", tr(STR_LBL_SONAR));
        else
            SEND("<tr><td class=\"ok\">" ST_TICK "</td><td>%s</td>"
                 "<td>&mdash;</td></tr>", tr(STR_LBL_SONAR));
    }
    if (soil_ready()) {
        float soil_mv, soil_pct;
        if (soil_last(&soil_mv, &soil_pct) && isfinite(soil_pct))
            SEND("<tr><td class=\"ok\">" ST_TICK "</td><td>%s</td>"
                 "<td>%.0f %% &middot; %.0f mV</td></tr>",
                 tr(STR_LBL_SOIL), soil_pct, soil_mv);
        else if (soil_last(&soil_mv, &soil_pct))
            SEND("<tr><td class=\"ok\">" ST_TICK "</td><td>%s</td>"
                 "<td>%.0f mV</td></tr>", tr(STR_LBL_SOIL), soil_mv);
        else
            SEND("<tr><td class=\"ok\">" ST_TICK "</td><td>%s</td>"
                 "<td>&mdash;</td></tr>", tr(STR_LBL_SOIL));
    }

    /* Operator counters (no health glyph — empty first cell). Uptime is
     * human-readable; motion/bursts/photos are lifetime totals. */
    {
        char up[24];
        fmt_uptime(up, sizeof(up), uptime_s);
        SEND(
            "<tr><td></td><td class=\"k\">%s</td><td class=\"v\">%" PRIu32 "</td></tr>"
            "<tr><td></td><td class=\"k\">%s</td><td class=\"v\">%" PRIu32 "</td></tr>"
            "<tr><td></td><td class=\"k\">%s</td><td class=\"v\">%" PRIu32 "</td></tr>"
            "<tr><td></td><td class=\"k\">%s</td><td class=\"v\">%s</td></tr>",
            tr(STR_S_MOTION), pir_count, tr(STR_S_BURSTS), audio_bursts,
            tr(STR_S_PHOTOS), photo_count, tr(STR_S_UPTIME), up);
    }
    SEND("</table>");

    /* ── Diagnostics (collapsed) — internals an operator rarely needs but a
     * dev/HIL might: the two pinned CPU1 tasks (audio + camera worker), heap
     * (now + worst-ever), HTTP-task stack high-water, and the scarce
     * internal/DMA pools. PSRAM can't serve DMA, so the DMA figure — not the
     * PSRAM-inclusive free heap — is what gates the BT/i2s/camera buffers (its
     * exhaustion is what broke the BLE bring-up). ── */
    {
        size_t heap_min = heap_caps_get_minimum_free_size(MALLOC_CAP_DEFAULT);
        UBaseType_t main_stack_hwm =
            uxTaskGetStackHighWaterMark(xTaskGetCurrentTaskHandle());
        SEND("<details><summary>%s</summary><table>", tr(STR_H_DIAGNOSTICS));
        SEND("<tr><td class=\"%s\">%s</td><td>%s</td><td>%s</td></tr>"
             "<tr><td class=\"%s\">%s</td><td>%s</td><td>%s</td></tr>",
             b_audio_task ? "ok" : "warn", b_audio_task ? ST_TICK : ST_DASH,
             tr(STR_LBL_AUDIO_TASK), b_audio_task ? tr(STR_D_TASK_OK10) : tr(STR_D_TASK_FAIL),
             b_cam_worker ? "ok" : "warn", b_cam_worker ? ST_TICK : ST_DASH,
             tr(STR_LBL_CAM_WORKER), b_cam_worker ? tr(STR_D_TASK_OK5) : tr(STR_D_TASK_FAIL));
        SEND("<tr><td class=\"k\">%s</td><td class=\"v\">%" PRIu32 " B (%s %zu B)</td></tr>"
             "<tr><td class=\"k\">%s</td><td class=\"v\">%u B</td></tr>"
             "<tr><td class=\"k\">int / DMA free</td>"
             "<td class=\"v\">%u / %u B (max %u)</td></tr>",
             tr(STR_S_FREE_HEAP), heap_free, tr(STR_S_HEAP_MINEVER), heap_min,
             tr(STR_S_HTTP_STACK), (unsigned)(main_stack_hwm * sizeof(StackType_t)),
             (unsigned)heap_caps_get_free_size(MALLOC_CAP_INTERNAL),
             (unsigned)heap_caps_get_free_size(MALLOC_CAP_DMA),
             (unsigned)heap_caps_get_largest_free_block(MALLOC_CAP_DMA));
        SEND("</table></details>");
    }

    /* ── BLE meters (UC96 / BTHome) — only when one is streaming or a BTHome
     * sensor has data. A separate table under the on-board sensors so the BLE
     * readings (off-board, allowlisted) stay visually distinct. Rows go via
     * sendstr_chunk (not SEND) so the values string sidesteps format-truncation. */
    if (ble_running()) {
        /* Heap, not a ~3 KB stack array (BLE_VIEW_MAX × sizeof(ble_dev_view_t)):
         * this runs on the 8 KB plain-HTTP task and the page already nests deep
         * (send_page_head + the status table + per-row buffers). bn=0 on alloc
         * failure makes the loops/render below no-op; rendered via sendstr_chunk
         * (no early return), so free() always runs. */
        ble_dev_view_t *bv = malloc(sizeof(*bv) * BLE_VIEW_MAX);
        int bn = bv ? ble_snapshot(bv, BLE_VIEW_MAX) : 0, show = 0;
        for (int i = 0; i < bn; i++)
            if (bv[i].conn_state == 3 || bv[i].has_bthome) show++;
        if (show) {
            httpd_resp_sendstr_chunk(req, "<h2>&#128268; BLE meters</h2><table>");
            for (int i = 0; i < bn; i++) {
                if (!(bv[i].conn_state == 3 || bv[i].has_bthome)) continue;
                char nm[BLE_STORE_NAME_CAP], nmesc[80], vv[160];
                if (!ble_store_get_name(bv[i].id, nm, sizeof(nm)) || !nm[0])
                    snprintf(nm, sizeof(nm), "%.12s", bv[i].id);  /* id is 12 hex */
                scan_html_escape(nm, nmesc, sizeof(nmesc));
                ble_values_html(&bv[i], vv, sizeof(vv));
                httpd_resp_sendstr_chunk(req, "<tr><td class=\"k\">");
                httpd_resp_sendstr_chunk(req, nmesc);
                httpd_resp_sendstr_chunk(req, "</td><td class=\"v\">");
                httpd_resp_sendstr_chunk(req, vv);
                httpd_resp_sendstr_chunk(req, "</td></tr>");
            }
            httpd_resp_sendstr_chunk(req, "</table>");
        }
        free(bv);
    }

    /* ── Device meta ──────────────────────────────────────────────────── */
    SEND(
        "<h2>%s</h2><table>"
        "<tr><td class=\"k\">MAC</td><td class=\"v\"><code>%s</code></td></tr>"
        "<tr><td class=\"k\">%s</td><td class=\"v\"><code>%s</code></td></tr>"
        "<tr><td class=\"k\">%s</td><td class=\"v\"><code>%s (IDF %s)</code></td></tr>"
        "</table>",
        tr(STR_H_DEVICE), mac, tr(STR_DEV_ID), device_id(), tr(STR_DEV_VERSION),
        app->version, app->idf_ver);

    /* ── Pin map (runtime, read from app_config) ──────────────────────── */
    SEND("<h2>%s</h2>"
         "<table>"
         "<tr><td class=\"k\">Slot</td><td class=\"k\">GPIO</td>"
         "<td class=\"k\">%s</td></tr>", tr(STR_H_PINMAP), tr(STR_PM_FUNCTION));
    for (int slot = 0; slot < app_config_pin_slot_count(); slot++) {
        int gpio = -1;
        const char *fn = "none";
        app_config_pin_slot_info(slot, &gpio, &fn);
        SEND("<tr><td class=\"v\"><code>D%d</code></td>"
             "<td class=\"v\"><code>GPIO%d</code></td>"
             "<td class=\"v\">%s<code>%s</code></td></tr>",
             slot, gpio, pin_fn_icon(fn), fn);
    }
    SEND("</table>");

    /* ── Endpoints + live mic + live cam ──────────────────────────────── */
    /* Split across multiple SEND chunks — one big literal overflows the
     * CHUNK_SZ (1 KB) format buffer. */
    SEND(
        "<h2>%s</h2><ul>"
        "<li><a href=\"/last.jpg\">/last.jpg</a> &mdash; %s</li>",
        tr(STR_H_ENDPOINTS), tr(STR_EP_LASTJPG));
    SEND(
        "<li><a href=\"/capture\">/capture</a> &mdash; %s</li>"
        "<li><code>/photo?d=&amp;f=</code> &mdash; %s</li>"
        "<li><a href=\"/photos\">/photos</a> &mdash; %s</li>"
        "<li><a href=\"/mic.wav\">/mic.wav</a> &mdash; %s</li>"
        "<li><a href=\"/stream.mjpg\">/stream.mjpg</a> &mdash; %s</li>"
        "<li><a href=\"/selftest\">/selftest</a> &mdash; %s</li>",
        tr(STR_EP_CAPTURE), tr(STR_EP_PHOTO), tr(STR_EP_PHOTOS), tr(STR_EP_MIC),
        tr(STR_EP_STREAM), tr(STR_EP_SELFTEST));
    SEND(
        "<li><a href=\"/i2c\">/i2c</a> &mdash; %s</li>"
        "<li><a href=\"/sensors\">/sensors</a> &mdash; live read of all registered I&sup2;C sensors</li>"
        "<li><a href=\"/oled/qr\">/oled/qr</a> &mdash; show a QR on the OLED (?text=...) for ~90s</li>"
        "<li><a href=\"/oled/logo\">/oled/logo</a> &mdash; upload a custom boot logo (image &rarr; 128&times;64)</li>"
        "<li><a href=\"/sht41/bus1\">/sht41/bus1</a> &mdash; %s</li>"
        "<li><a href=\"/max17048/bus1\">/max17048/bus1</a> &mdash; %s</li>"
        "<li><a href=\"/i2c/bus1_diag\">/i2c/bus1_diag</a> &mdash; %s</li>"
        "</ul>",
        tr(STR_EP_I2C), tr(STR_EP_SHT1), tr(STR_EP_MAX1), tr(STR_EP_I2CDIAG));
#if CONFIG_CHYTRA_BUDKA_DEBUG_ENDPOINTS
    SEND(
        "<h2>Debug endpoints</h2><ul>"
        "<li><a href=\"/debug/cores\">/debug/cores</a> &mdash; per-task core + runtime stats</li>"
        "<li><a href=\"/debug/pir\">/debug/pir</a> &mdash; raw PIR pin read + histogram</li>"
        "<li><a href=\"/debug/hang\">/debug/hang</a> &mdash; intentional WDT trigger (crash path test)</li>"
        "<li><a href=\"/debug/wifi_disconnect\">/debug/wifi_disconnect</a> &mdash; force STA disconnect</li>"
        "<li><a href=\"/debug/sd_format\">/debug/sd_format</a> &mdash; reformat SD (destructive)</li>"
        "<li><a href=\"/debug/sd_remount\">/debug/sd_remount</a> &mdash; remount SD without reboot</li>"
        "<li><code>POST /debug/uart_servo</code> &mdash; raw hex on the UART servo bus "
        "(<code>?timeout_ms=&lt;n&gt;</code>)</li>"
        "<li><code>POST /debug/capture</code> &mdash; enqueue a capture with operator-supplied "
        "trigger (body = trigger string, e.g. <code>pir</code>); used by EXIF HIL tests</li>"
        "<li><a href=\"/debug/tls_csr\">/debug/tls_csr</a> &mdash; fresh EC P-256 CSR PEM "
        "(pipe to <code>openssl req -text -noout</code> to inspect)</li>");
    SEND(
        "<li><a href=\"/debug/cam_standby?on=1\">/debug/cam_standby</a> &mdash; OV3660 "
        "software standby toggle (<code>?on=1|0</code>); bench power-measurement spike</li>"
        "</ul>");
#endif
    SEND("</body></html>");  /* live mic moved up under the photo/stream preview */

#undef SEND
#undef CHUNK_SZ
    httpd_resp_send_chunk(req, NULL, 0); /* finish chunked transfer */
    free(chunk);
    return ESP_OK;
}

static esp_err_t last_jpg_get(httpd_req_t *req) {
    HTTP_AUTH_OR_RETURN(req);
    size_t len = 0;
    uint8_t *buf = camera_last_jpeg_dup(&len);
    if (!buf) {
        /* esp-httpd's send_err emits text/html with no charset; browsers
         * default to ISO-8859-1 (RFC 7231 §3.1.1.5) and an em-dash here
         * shows as mojibake. Plain ASCII keeps the message readable
         * regardless of client charset assumption. */
        httpd_resp_send_err(req, HTTPD_404_NOT_FOUND,
                            "no capture yet -- POST /cmd/photo or wait for trigger");
        return ESP_OK;
    }
    httpd_resp_set_type(req, "image/jpeg");
    httpd_resp_set_hdr(req, "Cache-Control", "no-store");
    esp_err_t e = httpd_resp_send(req, (const char *)buf, len);
    free(buf);
    return e;
}

static atomic_bool s_capture_http_busy = false;  /* one async /capture at a time */

/* /capture runs ASYNC: camera_capture_event() blocks ~2-4 s (IR warm, sensor
 * capture, EXIF stamp); running it in the single httpd task stalled concurrent
 * page loads. Offload to a task; cap at one in flight. */
static void capture_task(void *arg) {
    httpd_req_t *req = (httpd_req_t *)arg;
    esp_err_t e = camera_capture_event("http");
    if (e == ESP_OK)
        last_jpg_get(req);  /* send the freshly-cached JPEG (re-checks auth: ok) */
    else
        httpd_resp_send_err(req, HTTPD_500_INTERNAL_SERVER_ERROR, "capture failed");
    atomic_store(&s_capture_http_busy, false);
    httpd_req_async_handler_complete(req);
    vTaskDeleteWithCaps(NULL);  /* PSRAM stack (WithCaps) — free it accordingly */
}

static esp_err_t capture_get(httpd_req_t *req) {
    HTTP_AUTH_OR_RETURN(req);
    if (!camera_ready()) {
        httpd_resp_send_err(req, HTTPD_500_INTERNAL_SERVER_ERROR, "camera not initialized");
        return ESP_OK;
    }
    if (atomic_exchange(&s_capture_http_busy, true)) {
        httpd_resp_set_status(req, "503 Service Unavailable");
        httpd_resp_set_type(req, "text/plain");
        httpd_resp_sendstr(req, "capture already in progress\n");
        return ESP_OK;
    }
    httpd_req_t *areq = NULL;
    if (httpd_req_async_handler_begin(req, &areq) != ESP_OK) {
        atomic_store(&s_capture_http_busy, false);
        httpd_resp_send_err(req, HTTPD_500_INTERNAL_SERVER_ERROR, "async begin failed");
        return ESP_OK;
    }
    /* 12 KB stack from PSRAM (WithCaps): BLE-on fragments internal DRAM to a
     * ~2-3 KB largest block so a normal (internal) 12 KB stack can't be
     * allocated; PSRAM has room. The task does camera_capture_event + a TLS
     * send — no flash-cache-disable ops — so a PSRAM stack is safe here. */
    if (xTaskCreatePinnedToCoreWithCaps(capture_task, "cap_http", 12288, areq, 5,
                                        NULL, tskNO_AFFINITY, MALLOC_CAP_SPIRAM) != pdPASS) {
        /* PSRAM exhausted (very unlikely) — respond 503 instead of silently
         * completing the async request (which would hang the client). */
        httpd_resp_set_status(areq, "503 Service Unavailable");
        httpd_resp_set_type(areq, "text/plain");
        httpd_resp_sendstr(areq, "capture unavailable (low memory; try with BLE off)\n");
        httpd_req_async_handler_complete(areq);
        atomic_store(&s_capture_http_busy, false);
        return ESP_OK;
    }
    return ESP_OK;
}

/* One-at-a-time gates for the two live streams. The streams are long
 * loops in the httpd task; two concurrent fetches of the same URL
 * (e.g., a refresh that didn't drop the prior connection, or two
 * tabs) leave the second request waiting on the http server while
 * the first holds the task slot. Returning 503 immediately keeps the
 * board healthy. */
static atomic_bool s_mic_busy = false;
static atomic_bool s_mjpg_busy = false;

/* Exported so app_config can check whether MJPEG is currently streaming
 * before deciding whether a cam_ / mjpg_ cfg change should apply right
 * now or be deferred to the next MJPEG-exit / next stream-open. Tying
 * the apply gate to "is the handler actively running" (not to a
 * cached s_active_profile flag in camera.c) avoids the persistent-leak
 * bug where a stream-profile flag survived past handler exit. */
bool http_server_mjpg_is_active(void) {
    return atomic_load(&s_mjpg_busy);
}

/* GET /mic.wav — live PCM stream, chunked Transfer-Encoding. Plays
 * until the client disconnects or the safety cap fires (default 60 s,
 * cap with ?max=<s> up to 3600). The ESP doesn't do DC removal /
 * gain / EQ here — raw int16 from the PDM ring straight to the wire.
 * Any cleanup belongs on the consumer side. */
static esp_err_t mic_wav_get(httpd_req_t *req) {
    HTTP_AUTH_OR_RETURN(req);
    if (!audio_ready()) {
        httpd_resp_send_err(req, HTTPD_500_INTERNAL_SERVER_ERROR, "mic not capturing yet");
        return ESP_OK;
    }
    if (atomic_exchange(&s_mic_busy, true)) {
        httpd_resp_set_status(req, "503 Service Unavailable");
        httpd_resp_set_type(req, "text/plain");
        httpd_resp_sendstr(req, "another mic stream is active\n");
        return ESP_OK;
    }

    float max_secs = 60.0f;  // matches the handler doc; ?max=<s> overrides up to 3600
    char qbuf[24];
    if (httpd_req_get_url_query_str(req, qbuf, sizeof(qbuf)) == ESP_OK) {
        char val[12];
        if (httpd_query_key_value(qbuf, "max", val, sizeof(val)) == ESP_OK) {
            float v = strtof(val, NULL);
            if (v > 0.0f && v <= 3600.0f)
                max_secs = v;
        }
    }

    httpd_resp_set_type(req, "audio/wav");
    httpd_resp_set_hdr(req, "Cache-Control", "no-store");

    /* 44-byte streaming WAV header (data_len = 0xFFFFFFFF). */
    uint8_t header[44];
    audio_wav_header_streaming(header, audio_sample_rate());
    if (httpd_resp_send_chunk(req, (const char *)header, sizeof(header)) != ESP_OK) {
        atomic_store(&s_mic_busy, false);
        return ESP_OK;
    }

    /* Start at the live edge — don't backfill stale samples from the
     * ring (the snapshot endpoint is /mic.wav?max=... if anyone wants
     * a fixed-length recording later). */
    uint32_t read_pos = audio_ring_write_pos();
    int16_t chunk[1024];  // 64 ms at 16 kHz; 2 KB on stack
    int64_t now0 = esp_timer_get_time();
    int64_t deadline_us = now0 + (int64_t)(max_secs * 1e6f);
    int64_t last_data_us = now0;  // last time the ring actually yielded samples

    /* End the stream if the mic produces nothing for this long. The audio
     * pump can stall or be disabled (VAD off, BLE-on starving the i2s DMA,
     * mic HW fault); without this cap the loop would hold the socket — and
     * the single s_mic_busy slot — open for the full max_secs. Mirrors the
     * "frame_null_cnt → break" pattern in IDF's streaming examples. */
    const int64_t MIC_STALL_US = 2 * 1000000LL;

    while (esp_timer_get_time() < deadline_us) {
        uint32_t next = read_pos;
        size_t got = audio_ring_read(read_pos, chunk, sizeof(chunk) / sizeof(chunk[0]), &next);
        if (got == 0) {
            /* Ring empty (or lock briefly contended). Two things matter here:
             *   1) We MUST yield. pdMS_TO_TICKS(8) rounds to 0 ticks at
             *      CONFIG_FREERTOS_HZ=100, and vTaskDelay(0) does not yield to
             *      lower-priority tasks — so the old code busy-spun at the
             *      httpd-task priority, starved the main loop + IDLE0 on CPU0,
             *      and tripped the task watchdog (root cause of the v0.4.4
             *      `task_wdt` reboots). cb_delay_ms() floors at one tick so it
             *      always yields. See cb_time.h.
             *   2) Bail out if the mic has been silent too long (stall-cap). */
            if (esp_timer_get_time() - last_data_us > MIC_STALL_US) {
                ESP_LOGW(TAG, "/mic.wav: no audio for %llds — ending stream",
                         (long long)(MIC_STALL_US / 1000000));
                break;
            }
            cb_delay_ms(8);  // ≥1 tick (10 ms) — close to real-time, never a spin
            continue;
        }
        last_data_us = esp_timer_get_time();
        read_pos = next;
        if (httpd_resp_send_chunk(req, (const char *)chunk, got * sizeof(int16_t)) != ESP_OK)
            break;  // client disconnected
    }
    httpd_resp_send_chunk(req, NULL, 0);  // end chunked stream
    atomic_store(&s_mic_busy, false);
    return ESP_OK;
}

/* qsort comparator: descending string compare. Filenames are
 * YYYY-MM-DD_HH-MM-SS_<mac>_<tag>.jpg (Europe/Prague local time) so
 * lexicographic descending = chronologically newest first. */
static int photo_name_cmp_desc(const void *a, const void *b) {
    return strcmp(*(const char *const *)b, *(const char *const *)a);
}

/* GET /stream.mjpg — multipart MJPEG live preview. Native browser
 * support: just open the URL in any browser, or point VLC at it.
 *
 * The sensor swaps from the "capture" profile (cam_framesize +
 * cam_quality) to the "stream" profile (mjpg_framesize + mjpg_quality)
 * on entry and restores capture profile on every exit path. Stream
 * profile is typically lighter (e.g. SVGA q=18) so the live preview is
 * faster while stills stay sharp. No mid-stream toggling — if VAD/PIR
 * fires a triggered capture during the stream, the resulting JPEG
 * comes out at stream quality; event/photo JSON publishes the actual
 * (framesize, quality) so HA can correlate.
 *
 * 5 min default cap (overridable via ?max=N up to 3600) so a forgotten
 * browser tab doesn't keep the sensor pinned in stream profile.
 *
 * Runs ASYNC: esp-httpd is single-threaded, so this multi-minute loop would
 * monopolize the one httpd task and block EVERY other request until the
 * stream ended (bench-confirmed: a GET / hung ~14 s behind an open stream).
 * httpd_req_async_handler_begin() hands the socket to stream_mjpg_task and
 * frees the httpd worker immediately. s_mjpg_busy caps it at one stream, so
 * at most one extra task + one held socket. */
typedef struct {
    httpd_req_t *req;
    int64_t      deadline_us;
} mjpg_async_t;

static void stream_mjpg_task(void *arg) {
    mjpg_async_t *a = (mjpg_async_t *)arg;
    httpd_req_t *req = a->req;
    int64_t deadline_us = a->deadline_us;
    free(a);

    httpd_resp_set_type(req, "multipart/x-mixed-replace; boundary=frame");
    httpd_resp_set_hdr(req, "Cache-Control", "no-store");
    httpd_resp_set_hdr(req, "X-Framerate", "best-effort");

    char part_hdr[96];
    while (esp_timer_get_time() < deadline_us) {
        /* Standalone heap copy under the sensor mutex (camera_grab_jpeg_copy):
         * serializes the grab against a concurrent /capture and lets us send
         * the slow TLS copy without holding the sensor locked. */
        uint8_t *jpg = NULL;
        size_t jlen = camera_grab_jpeg_copy(&jpg);
        if (!jlen) {
            vTaskDelay(pdMS_TO_TICKS(100));
            continue;
        }
        int hn = snprintf(part_hdr, sizeof(part_hdr),
                          "\r\n--frame\r\n"
                          "Content-Type: image/jpeg\r\n"
                          "Content-Length: %u\r\n\r\n",
                          (unsigned)jlen);
        esp_err_t e1 = httpd_resp_send_chunk(req, part_hdr, hn);
        esp_err_t e2 =
            (e1 == ESP_OK) ? httpd_resp_send_chunk(req, (const char *)jpg, jlen) : ESP_FAIL;
        free(jpg);
        if (e1 != ESP_OK || e2 != ESP_OK)
            break;  // client disconnected
        vTaskDelay(pdMS_TO_TICKS(10));
    }
    httpd_resp_send_chunk(req, NULL, 0);
    /* Restore capture profile + clear busy on every exit, then return the
     * socket to httpd. */
    (void)camera_apply_capture_profile();
    atomic_store(&s_mjpg_busy, false);
    httpd_req_async_handler_complete(req);
    vTaskDeleteWithCaps(NULL);  /* PSRAM stack (WithCaps) */
}

static esp_err_t stream_mjpg_get(httpd_req_t *req) {
    HTTP_AUTH_OR_RETURN(req);
    if (!camera_ready()) {
        httpd_resp_send_err(req, HTTPD_500_INTERNAL_SERVER_ERROR, "camera not ready");
        return ESP_OK;
    }
    if (atomic_exchange(&s_mjpg_busy, true)) {
        httpd_resp_set_status(req, "503 Service Unavailable");
        httpd_resp_set_type(req, "text/plain");
        httpd_resp_sendstr(req, "another mjpg stream is active\n");
        return ESP_OK;
    }

    /* Switch to stream profile. The profile-apply contends with an
     * in-flight capture for the sensor mutex; that hold is now short
     * (capture moved SD/MQTT outside it), but a capture can still be
     * mid-SCCB when the operator opens the stream — exactly the field
     * positioning case (step in front → PIR capture → open stream). So
     * retry a few times before giving up, instead of 500ing on the first
     * collision. ~5×600 ms covers a capture's sensor window with margin. */
    esp_err_t pe = ESP_FAIL;
    for (int attempt = 0; attempt < 5; attempt++) {
        pe = camera_apply_stream_profile();
        if (pe == ESP_OK) break;
        vTaskDelay(pdMS_TO_TICKS(600));
    }
    if (pe != ESP_OK) {
        atomic_store(&s_mjpg_busy, false);
        httpd_resp_send_err(req, HTTPD_500_INTERNAL_SERVER_ERROR, "stream profile apply failed");
        return ESP_OK;
    }

    /* 5 min default cap; ?max=N (<=3600) override. Parse here while we still
     * hold the original request, then hand off to the worker task. */
    int64_t max_us = 300LL * 1000 * 1000;
    char qbuf[24];
    if (httpd_req_get_url_query_str(req, qbuf, sizeof(qbuf)) == ESP_OK) {
        char val[12];
        if (httpd_query_key_value(qbuf, "max", val, sizeof(val)) == ESP_OK) {
            float v = strtof(val, NULL);
            if (v > 0.0f && v <= 3600.0f)
                max_us = (int64_t)(v * 1e6f);
        }
    }

    /* Detach the socket to a worker task so the single httpd task stays free
     * to serve everyone else. On any failure after the profile switch, undo
     * it + clear busy so the server isn't left wedged in stream profile. */
    httpd_req_t *areq = NULL;
    if (httpd_req_async_handler_begin(req, &areq) != ESP_OK) {
        (void)camera_apply_capture_profile();
        atomic_store(&s_mjpg_busy, false);
        httpd_resp_send_err(req, HTTPD_500_INTERNAL_SERVER_ERROR, "async begin failed");
        return ESP_OK;
    }
    mjpg_async_t *a = (mjpg_async_t *)malloc(sizeof(*a));
    if (!a) {
        httpd_req_async_handler_complete(areq);
        (void)camera_apply_capture_profile();
        atomic_store(&s_mjpg_busy, false);
        return ESP_OK;
    }
    a->req = areq;
    a->deadline_us = esp_timer_get_time() + max_us;
    /* 8 KB stack from PSRAM (WithCaps) — see capture_get: an internal 8 KB stack
     * can't be allocated BLE-on (fragmented to ~2-3 KB); PSRAM has room. ssl_write
     * + camera_grab_jpeg_copy (heap) + snprintf — no flash-cache-disable ops. */
    if (xTaskCreatePinnedToCoreWithCaps(stream_mjpg_task, "mjpg_stream", 8192, a, 5,
                                        NULL, tskNO_AFFINITY, MALLOC_CAP_SPIRAM) != pdPASS) {
        /* PSRAM exhausted (very unlikely) — respond 503 instead of hanging. */
        free(a);
        httpd_resp_set_status(areq, "503 Service Unavailable");
        httpd_resp_set_type(areq, "text/plain");
        httpd_resp_sendstr(areq, "stream unavailable (low memory; try with BLE off)\n");
        httpd_req_async_handler_complete(areq);
        (void)camera_apply_capture_profile();
        atomic_store(&s_mjpg_busy, false);
        return ESP_OK;
    }
    return ESP_OK;  /* httpd worker freed immediately; task owns the socket */
}

static esp_err_t selftest_get(httpd_req_t *req) {
    HTTP_AUTH_OR_RETURN(req);
    char json[704];  /* match selftest_run_and_publish()'s buffer */
    selftest_run_and_publish(json, sizeof(json));
    httpd_resp_set_type(req, "application/json; charset=utf-8");
    return httpd_resp_send(req, json, strlen(json));
}

/* ── photo store browsing (date-tree) ───────────────────────────────────────
 * Photos live under /sdcard as day buckets (YYYY-MM-DD/, plus boot/ for
 * pre-clock captures and loose legacy *.jpg as the "root" bucket — see
 * sd_layout.h). The gallery lists buckets first (cheap: one readdir of the
 * card root) and walks a single day's directory only when you open it, so the
 * listing cost no longer scales with the whole-card photo count. A one-entry
 * PSRAM cache keyed on (bucket, sd_storage_listing_gen) keeps paging within a
 * day from re-reading the card; it's invalidated whenever a capture or
 * autoprune changes the set. Still no thumbnails — the browser renders the
 * full JPEG that /photo serves (now cacheable + range-able). */

/* Newest-first ordering of bucket names for the day index. */
static int bucket_cmp_newest_first(const void *a, const void *b) {
    return -sd_layout_bucket_cmp_oldest_first(*(const char *const *)a,
                                              *(const char *const *)b);
}

static char *dup_str(const char *s) {
    size_t n = strlen(s) + 1;
    char *p = malloc(n);
    if (p) memcpy(p, s, n);
    return p;
}

/* Minimal JSON string-body escaper: backslash, double-quote, and control
 * chars (<0x20) → \uXXXX. Firmware-written filenames never need this (they're
 * [A-Za-z0-9._-]), but a file dropped on the card out-of-band could otherwise
 * break the /photos.json output. Truncates safely if `out` is too small. */
static void json_escape_str(const char *s, char *out, size_t cap) {
    size_t o = 0;
    for (; *s && o + 7 < cap; s++) {
        unsigned char c = (unsigned char)*s;
        if (c == '"' || c == '\\') {
            out[o++] = '\\';
            out[o++] = (char)c;
        } else if (c < 0x20) {
            int k = snprintf(out + o, cap - o, "\\u%04x", c);
            if (k > 0) o += (size_t)k;
        } else {
            out[o++] = (char)c;
        }
    }
    out[o] = '\0';
}

/* One-entry listing cache: the sorted (desc) leaf names of a single bucket. */
static SemaphoreHandle_t s_listing_mtx = NULL;
static char     s_lc_bucket[SD_LAYOUT_DAY_LEN] = {0};
static uint32_t s_lc_gen = 0;
static bool     s_lc_valid = false;
static char   **s_lc_names = NULL;
static size_t   s_lc_count = 0;

static void listing_cache_clear_locked(void) {
    if (s_lc_names) {
        for (size_t i = 0; i < s_lc_count; i++) free(s_lc_names[i]);
        free(s_lc_names);
    }
    s_lc_names = NULL;
    s_lc_count = 0;
    s_lc_valid = false;
    s_lc_bucket[0] = '\0';
}

/* (Re)build the cache for `bucket` at the current generation. Lock held. */
static size_t listing_cache_ensure_locked(const char *bucket) {
    uint32_t gen = sd_storage_listing_gen();
    if (s_lc_valid && gen == s_lc_gen && strcmp(bucket, s_lc_bucket) == 0)
        return s_lc_count;
    listing_cache_clear_locked();

    bool is_root = (strcmp(bucket, SD_LAYOUT_ROOT) == 0);
    char dirpath[32];
    if (is_root) snprintf(dirpath, sizeof(dirpath), "%s", SD_MOUNT_POINT);
    else         snprintf(dirpath, sizeof(dirpath), "%s/%s", SD_MOUNT_POINT, bucket);

    DIR *d = opendir(dirpath);
    if (!d) {
        /* Transient SD glitch (vs a genuinely empty/openable dir) — DON'T stamp
         * the cache valid, or a populated day would show empty until the next
         * gen bump. Leave it invalid so the next request retries the open. */
        return 0;
    }
    size_t cap = 128, count = 0;
    char **names = heap_caps_malloc(cap * sizeof(char *), MALLOC_CAP_SPIRAM);
    if (!names) names = malloc(cap * sizeof(char *));
    struct dirent *e;
    while (names && (e = readdir(d)) != NULL) {
        const char *nm = e->d_name;
        if (is_root) {
            if (sd_layout_classify(nm) != SD_BUCKET_ROOT_JPG) continue;
        } else {
            size_t nl = strlen(nm);
            if (nl < 4 || strcasecmp(nm + nl - 4, ".jpg") != 0) continue;
        }
        if (count == cap) {
            size_t nc = cap * 2;
            char **g = heap_caps_realloc(names, nc * sizeof(char *), MALLOC_CAP_SPIRAM);
            if (!g) g = realloc(names, nc * sizeof(char *));
            if (!g) break;
            names = g;
            cap = nc;
        }
        size_t nl = strlen(nm);
        char *dup = heap_caps_malloc(nl + 1, MALLOC_CAP_SPIRAM);
        if (!dup) break;
        memcpy(dup, nm, nl + 1);
        names[count++] = dup;
    }
    closedir(d);
    if (names && count > 1)
        qsort(names, count, sizeof(char *), photo_name_cmp_desc);
    /* Stamp the cache valid only after a successful scan (an empty-but-openable
     * dir caches as 0; a failed open above did not get here). */
    s_lc_names = names;
    s_lc_count = count;
    strncpy(s_lc_bucket, bucket, sizeof(s_lc_bucket) - 1);
    s_lc_bucket[sizeof(s_lc_bucket) - 1] = '\0';
    s_lc_gen = gen;
    s_lc_valid = true;
    return count;
}

/* Copy one page's leaf names for `bucket` into out[] (each malloc'd; caller
 * frees). Returns count copied; *total = full bucket count. The cache lock is
 * held across the readdir/sort + slice copy only — never across a network
 * send, so a slow client can't block another listing request for seconds. */
static size_t listing_page(const char *bucket, int page, int per_page,
                           char **out, size_t out_cap, size_t *total) {
    if (total) *total = 0;
    if (!s_listing_mtx) return 0;
    xSemaphoreTake(s_listing_mtx, portMAX_DELAY);
    size_t count = listing_cache_ensure_locked(bucket);
    if (total) *total = count;
    size_t start, end;
    sd_layout_page_slice(count, page, per_page, &start, &end);
    size_t n = 0;
    for (size_t i = start; i < end && n < out_cap; i++) {
        char *dup = dup_str(s_lc_names[i]);
        if (!dup) break;
        out[n++] = dup;
    }
    xSemaphoreGive(s_listing_mtx);
    return n;
}

/* List the buckets present under the card root, newest-first. out[] entries
 * malloc'd (caller frees). Returns count (capped at out_cap). */
static size_t list_buckets(char **out, size_t out_cap) {
    DIR *d = opendir(SD_MOUNT_POINT);
    if (!d) return 0;
    size_t n = 0;
    bool boot_seen = false, root_seen = false;
    struct dirent *e;
    while ((e = readdir(d)) != NULL) {
        sd_bucket_kind_t k = sd_layout_classify(e->d_name);
        if (k == SD_BUCKET_DATE) {
            if (n < out_cap) {
                char *dup = dup_str(e->d_name);
                if (dup) out[n++] = dup;
            }
        } else if (k == SD_BUCKET_BOOT) {
            boot_seen = true;
        } else if (k == SD_BUCKET_ROOT_JPG) {
            root_seen = true;
        }
    }
    closedir(d);
    if (boot_seen && n < out_cap) { char *p = dup_str(SD_LAYOUT_BOOT_DIR); if (p) out[n++] = p; }
    if (root_seen && n < out_cap) { char *p = dup_str(SD_LAYOUT_ROOT);     if (p) out[n++] = p; }
    if (n > 1) qsort(out, n, sizeof(char *), bucket_cmp_newest_first);
    return n;
}

/* Human label for a bucket in the gallery (dates shown verbatim). */
static const char *bucket_label(const char *bucket) {
    if (strcmp(bucket, SD_LAYOUT_ROOT) == 0) return tr(STR_PH_ROOT_BUCKET);
    if (strcmp(bucket, SD_LAYOUT_BOOT_DIR) == 0) return tr(STR_PH_BOOT_BUCKET);
    return bucket;
}

#define PHOTOS_PER_PAGE 100
static esp_err_t photos_get(httpd_req_t *req) {
    HTTP_AUTH_OR_RETURN(req);
    httpd_resp_set_type(req, "text/html; charset=utf-8");

    if (!sd_storage_ready()) {
        char m[220];
        snprintf(m, sizeof(m),
            "<!doctype html><meta charset=utf-8><link rel=stylesheet href=/style.css>"
            "<title>Chytr\xc3\xa1 Budka</title><body><p>%s</p>", tr(STR_PH_SD_UNMOUNTED));
        return httpd_resp_sendstr(req, m);
    }

    /* ?day=<bucket> selects one day; absent → the day index. ?page=N within. */
    char day[SD_LAYOUT_DAY_LEN] = {0};
    int  page = 0;
    {
        char q[48], v[16];
        if (httpd_req_get_url_query_str(req, q, sizeof(q)) == ESP_OK) {
            if (httpd_query_key_value(q, "day", v, sizeof(v)) == ESP_OK &&
                sd_layout_valid_day_param(v)) {
                strncpy(day, v, sizeof(day) - 1);
                day[sizeof(day) - 1] = '\0';
            }
            if (httpd_query_key_value(q, "page", v, sizeof(v)) == ESP_OK) {
                int p = atoi(v);
                if (p > 0) page = p;
            }
        }
    }

    char hdr[1280];

    /* ── Day index: list buckets, newest first (one readdir of the root). ── */
    if (day[0] == '\0') {
        int hn = snprintf(hdr, sizeof(hdr),
                 "<!doctype html><html><head><meta charset=\"utf-8\">"
                 "<meta name=\"viewport\" content=\"width=device-width,initial-scale=1\">"
                 "<title>Photos — %s</title>"
                 "<meta name=\"color-scheme\" content=\"dark\">"
                 "<link rel=\"stylesheet\" href=\"/style.css\"></head><body>"
                 "<h1>%s</h1><p><a href=\"/\">%s</a></p><table>",
                 device_id_suffix(), tr(STR_PH_TITLE), tr(STR_PH_BACK));
        httpd_resp_send_chunk(req, hdr, hn);
        send_security_banner(req);

        size_t bcap = 800;
        char **buckets = (char **)malloc(bcap * sizeof(char *));
        size_t bn = buckets ? list_buckets(buckets, bcap) : 0;
        char row[256];
        for (size_t i = 0; i < bn; i++) {
            int rn = snprintf(row, sizeof(row),
                              "<tr><td><a href=\"/photos?day=%s\">%s</a></td></tr>",
                              buckets[i], bucket_label(buckets[i]));
            if (rn > 0) httpd_resp_send_chunk(req, row, rn);
            free(buckets[i]);
        }
        free(buckets);
        if (bn == 0) {
            char empty[120];
            snprintf(empty, sizeof(empty), "<tr><td class=\"empty\">%s</td></tr>",
                     tr(STR_PH_EMPTY));
            httpd_resp_send_chunk(req, empty, strlen(empty));
        }
        httpd_resp_send_chunk(req, "</table></body></html>", 22);
        httpd_resp_send_chunk(req, NULL, 0);
        return ESP_OK;
    }

    /* ── One day's photos: readdir only that bucket (cached). ─────────────── */
    int hn = snprintf(hdr, sizeof(hdr),
             "<!doctype html><html><head><meta charset=\"utf-8\">"
             "<meta name=\"viewport\" content=\"width=device-width,initial-scale=1\">"
             "<title>%s — %s</title>"
             "<meta name=\"color-scheme\" content=\"dark\">"
             "<link rel=\"stylesheet\" href=\"/style.css\"></head><body>"
             "<h1>%s <small>%s</small></h1>"
             "<p><a href=\"/photos\">%s</a> &middot; <a href=\"/\">%s</a></p><table>",
             bucket_label(day), device_id_suffix(),
             tr(STR_PH_TITLE), bucket_label(day),
             tr(STR_PH_ALL_DAYS), tr(STR_PH_BACK));
    httpd_resp_send_chunk(req, hdr, hn);
    send_security_banner(req);

    char *names[PHOTOS_PER_PAGE];
    size_t total = 0;
    size_t n = listing_page(day, page, PHOTOS_PER_PAGE, names, PHOTOS_PER_PAGE, &total);

    char row[400];
    for (size_t i = 0; i < n; i++) {
        const char *name = names[i];
        char path[180];
        if (strcmp(day, SD_LAYOUT_ROOT) == 0)
            snprintf(path, sizeof(path), "%s/%s", SD_MOUNT_POINT, name);
        else
            snprintf(path, sizeof(path), "%s/%s/%s", SD_MOUNT_POINT, day, name);
        struct stat st;
        long long size = (stat(path, &st) == 0) ? (long long)st.st_size : 0;
        char trig[16];
        sd_layout_trigger_of(name, trig, sizeof(trig));
        /* HTML-escape the readdir-sourced name + trig: firmware names are
         * charset-safe, but a file placed on the card out-of-band could carry
         * HTML metacharacters and reflect into this auth-gated page. */
        char esc_name[160], esc_trig[40];
        scan_html_escape(name, esc_name, sizeof(esc_name));
        scan_html_escape(trig, esc_trig, sizeof(esc_trig));
        int rn = snprintf(row, sizeof(row),
                          "<tr><td><a href=\"/view?d=%s&amp;f=%s\">%s</a></td>"
                          "<td class=\"tag\">%s</td>"
                          "<td class=\"size\">%lld B</td></tr>",
                          day, esc_name, esc_name, esc_trig, size);
        if (rn > 0) httpd_resp_send_chunk(req, row, rn);
        free(names[i]);
    }
    if (total == 0) {
        char empty[120];
        snprintf(empty, sizeof(empty), "<tr><td class=\"empty\">%s</td></tr>", tr(STR_PH_EMPTY));
        httpd_resp_send_chunk(req, empty, strlen(empty));
    }

    /* Pagination footer (links carry the day). */
    size_t start, end;
    sd_layout_page_slice(total, page, PHOTOS_PER_PAGE, &start, &end);
    size_t total_pages = (total + PHOTOS_PER_PAGE - 1) / PHOTOS_PER_PAGE;
    if (total_pages == 0) total_pages = 1;
    char foot[512];
    int fn = snprintf(foot, sizeof(foot), "</table><p>%zu %s", total, tr(STR_PH_COUNT));
    if (total > 0) {
        fn += snprintf(foot + fn, sizeof(foot) - fn,
                       " &mdash; %s %zu&ndash;%zu (page %d / %zu)",
                       tr(STR_PH_SHOWING), start + 1, end, page + 1, total_pages);
    }
    fn += snprintf(foot + fn, sizeof(foot) - fn, ".</p><p>");
    if (page > 0) {
        fn += snprintf(foot + fn, sizeof(foot) - fn,
                       "<a href=\"/photos?day=%s&amp;page=%d\">%s</a>",
                       day, page - 1, tr(STR_PH_NEWER));
    }
    if (page > 0 && (size_t)(page + 1) < total_pages) {
        fn += snprintf(foot + fn, sizeof(foot) - fn, " &middot; ");
    }
    if ((size_t)(page + 1) < total_pages) {
        fn += snprintf(foot + fn, sizeof(foot) - fn,
                       "<a href=\"/photos?day=%s&amp;page=%d\">%s</a>",
                       day, page + 1, tr(STR_PH_OLDER));
    }
    fn += snprintf(foot + fn, sizeof(foot) - fn, "</p></body></html>");
    httpd_resp_send_chunk(req, foot, fn);
    httpd_resp_send_chunk(req, NULL, 0);
    return ESP_OK;
}

/* GET /photos.json — machine-readable listing for a JS/HA client.
 *   no ?day  → {"gen":G,"days":["2026-06-04",…,"boot","root"]}
 *   ?day=X   → {"day":"X","page":P,"per_page":N,"total":T,"pages":PP,
 *               "files":[{"f":"…","trig":"pir","bytes":123},…]}
 * The day index carries no per-day counts on purpose: counting would re-walk
 * every bucket and defeat the whole point of the tree. A client wanting counts
 * fetches a day, whose readdir is bounded. */
static esp_err_t photos_json_get(httpd_req_t *req) {
    HTTP_AUTH_OR_RETURN(req);
    httpd_resp_set_type(req, "application/json; charset=utf-8");
    if (!sd_storage_ready()) {
        httpd_resp_set_status(req, "503 Service Unavailable");
        return httpd_resp_sendstr(req, "{\"error\":\"sd not mounted\"}");
    }

    char day[SD_LAYOUT_DAY_LEN] = {0};
    int page = 0;
    {
        char q[48], v[16];
        if (httpd_req_get_url_query_str(req, q, sizeof(q)) == ESP_OK) {
            if (httpd_query_key_value(q, "day", v, sizeof(v)) == ESP_OK &&
                sd_layout_valid_day_param(v)) {
                strncpy(day, v, sizeof(day) - 1);
                day[sizeof(day) - 1] = '\0';
            }
            if (httpd_query_key_value(q, "page", v, sizeof(v)) == ESP_OK) {
                int p = atoi(v);
                if (p > 0) page = p;
            }
        }
    }

    char buf[256];
    if (day[0] == '\0') {
        int n0 = snprintf(buf, sizeof(buf), "{\"gen\":%" PRIu32 ",\"days\":[",
                          sd_storage_listing_gen());
        httpd_resp_send_chunk(req, buf, n0);
        size_t bcap = 800;
        char **buckets = (char **)malloc(bcap * sizeof(char *));
        size_t bn = buckets ? list_buckets(buckets, bcap) : 0;
        for (size_t i = 0; i < bn; i++) {
            int rn = snprintf(buf, sizeof(buf), "%s\"%s\"", i ? "," : "", buckets[i]);
            httpd_resp_send_chunk(req, buf, rn);
            free(buckets[i]);
        }
        free(buckets);
        httpd_resp_send_chunk(req, "]}", 2);
        httpd_resp_send_chunk(req, NULL, 0);
        return ESP_OK;
    }

    char *names[PHOTOS_PER_PAGE];
    size_t total = 0;
    size_t n = listing_page(day, page, PHOTOS_PER_PAGE, names, PHOTOS_PER_PAGE, &total);
    size_t total_pages = (total + PHOTOS_PER_PAGE - 1) / PHOTOS_PER_PAGE;
    if (total_pages == 0) total_pages = 1;
    int n0 = snprintf(buf, sizeof(buf),
                      "{\"day\":\"%s\",\"page\":%d,\"per_page\":%d,\"total\":%zu,"
                      "\"pages\":%zu,\"files\":[",
                      day, page, PHOTOS_PER_PAGE, total, total_pages);
    httpd_resp_send_chunk(req, buf, n0);
    for (size_t i = 0; i < n; i++) {
        const char *name = names[i];
        char path[180];
        if (strcmp(day, SD_LAYOUT_ROOT) == 0)
            snprintf(path, sizeof(path), "%s/%s", SD_MOUNT_POINT, name);
        else
            snprintf(path, sizeof(path), "%s/%s/%s", SD_MOUNT_POINT, day, name);
        struct stat st;
        long long size = (stat(path, &st) == 0) ? (long long)st.st_size : 0;
        char trig[16];
        sd_layout_trigger_of(name, trig, sizeof(trig));
        char esc_name[160], esc_trig[40];
        json_escape_str(name, esc_name, sizeof(esc_name));
        json_escape_str(trig, esc_trig, sizeof(esc_trig));
        int rn = snprintf(buf, sizeof(buf),
                          "%s{\"f\":\"%s\",\"trig\":\"%s\",\"bytes\":%lld}",
                          i ? "," : "", esc_name, esc_trig, size);
        httpd_resp_send_chunk(req, buf, rn);
        free(names[i]);
    }
    httpd_resp_send_chunk(req, "]}", 2);
    httpd_resp_send_chunk(req, NULL, 0);
    return ESP_OK;
}

/* GET /photo?d=<bucket>&f=<leaf> — serve one JPEG from the date-tree. d
 * defaults to "root" (legacy flat files); both components are validated
 * (no '/', no "..") so a caller can't escape /sdcard. Photos are immutable,
 * so the response is cacheable with an ETag (conditional GET → 304) and a
 * single Range request returns 206 so a client can resume over a weak link. */
static esp_err_t photo_get(httpd_req_t *req) {
    HTTP_AUTH_OR_RETURN(req);
    char qbuf[128], fname[80], dparam[16] = SD_LAYOUT_ROOT;
    if (httpd_req_get_url_query_str(req, qbuf, sizeof(qbuf)) != ESP_OK ||
        httpd_query_key_value(qbuf, "f", fname, sizeof(fname)) != ESP_OK) {
        httpd_resp_send_err(req, HTTPD_400_BAD_REQUEST, "missing ?f=");
        return ESP_OK;
    }
    {
        char v[16];
        if (httpd_query_key_value(qbuf, "d", v, sizeof(v)) == ESP_OK) {
            if (!sd_layout_valid_day_param(v)) {
                httpd_resp_send_err(req, HTTPD_400_BAD_REQUEST, "bad ?d=");
                return ESP_OK;
            }
            strncpy(dparam, v, sizeof(dparam) - 1);
            dparam[sizeof(dparam) - 1] = '\0';
        }
    }
    if (!sd_layout_valid_leaf(fname)) {
        httpd_resp_send_err(req, HTTPD_400_BAD_REQUEST, "filename: alphanumerics + . _ - only");
        return ESP_OK;
    }
    char path[180];
    if (strcmp(dparam, SD_LAYOUT_ROOT) == 0)
        snprintf(path, sizeof(path), "%s/%s", SD_MOUNT_POINT, fname);
    else
        snprintf(path, sizeof(path), "%s/%s/%s", SD_MOUNT_POINT, dparam, fname);

    /* Use low-level open()/read() — stdio fread() on this FATFS port was
     * returning errno=EIO consistently at 32 KB (= 2 × 16 KB cluster)
     * boundary, suggesting stdio's read-ahead buffering interacts
     * badly with the SDIO 1-bit driver. read() doesn't buffer ahead. */
    int fd = open(path, O_RDONLY);
    if (fd < 0) {
        httpd_resp_send_err(req, HTTPD_404_NOT_FOUND, "not on /sdcard");
        return ESP_OK;
    }
    struct stat st;
    off_t fsize = (fstat(fd, &st) == 0) ? st.st_size : 0;

    /* ETag = leaf + size; a stored photo never changes. */
    char etag[96];
    snprintf(etag, sizeof(etag), "\"%s-%lld\"", fname, (long long)fsize);

    char inm[96];
    if (httpd_req_get_hdr_value_str(req, "If-None-Match", inm, sizeof(inm)) == ESP_OK &&
        strcmp(inm, etag) == 0) {
        close(fd);
        httpd_resp_set_status(req, "304 Not Modified");
        httpd_resp_set_hdr(req, "ETag", etag);
        httpd_resp_set_hdr(req, "Cache-Control", "public, max-age=31536000, immutable");
        return httpd_resp_send(req, NULL, 0);
    }

    httpd_resp_set_type(req, "image/jpeg");
    httpd_resp_set_hdr(req, "Cache-Control", "public, max-age=31536000, immutable");
    httpd_resp_set_hdr(req, "ETag", etag);
    httpd_resp_set_hdr(req, "Accept-Ranges", "bytes");

    /* Optional single Range: bytes=A-[B]. */
    off_t start = 0, end = (fsize > 0) ? fsize - 1 : 0;
    bool ranged = false;
    char rng[64];
    if (fsize > 0 &&
        httpd_req_get_hdr_value_str(req, "Range", rng, sizeof(rng)) == ESP_OK &&
        strncmp(rng, "bytes=", 6) == 0) {
        const char *p = rng + 6;
        const char *dash = strchr(p, '-');
        if (dash) {
            long long a = (p != dash) ? atoll(p) : 0;
            long long b = (*(dash + 1)) ? atoll(dash + 1) : (long long)(fsize - 1);
            if (a >= fsize) {
                close(fd);
                char cr[48];
                snprintf(cr, sizeof(cr), "bytes */%lld", (long long)fsize);
                httpd_resp_set_status(req, "416 Range Not Satisfiable");
                httpd_resp_set_hdr(req, "Content-Range", cr);
                return httpd_resp_send(req, NULL, 0);
            }
            if (a < 0) a = 0;
            if (b > fsize - 1) b = fsize - 1;
            if (a <= b) {
                start = (off_t)a;
                end = (off_t)b;
                ranged = true;
            }
        }
    }
    if (ranged) {
        httpd_resp_set_status(req, "206 Partial Content");
        char cr[64];
        snprintf(cr, sizeof(cr), "bytes %lld-%lld/%lld",
                 (long long)start, (long long)end, (long long)fsize);
        httpd_resp_set_hdr(req, "Content-Range", cr);
        if (start > 0) lseek(fd, start, SEEK_SET);
    }

    char *buf = (char *)scratch_alloc(4096);
    if (!buf) {
        close(fd);
        httpd_resp_send_err(req, HTTPD_500_INTERNAL_SERVER_ERROR, "no mem");
        return ESP_OK;
    }
    off_t remaining = (fsize > 0) ? (end - start + 1) : 0;
    while (remaining > 0) {
        size_t want = (remaining > 4096) ? 4096 : (size_t)remaining;
        ssize_t rd = read(fd, buf, want);
        if (rd < 0) {
            if (errno == EINTR) continue;  /* not a truncation — retry */
            ESP_LOGW(TAG, "/photo %s: read errno=%d with %lld B left",
                     fname, errno, (long long)remaining);
            break;
        }
        if (rd == 0) break;  /* unexpected EOF (file shrank under us) */
        if (httpd_resp_send_chunk(req, buf, rd) != ESP_OK) {
            ESP_LOGW(TAG, "/photo %s: send_chunk failed", fname);
            break;
        }
        remaining -= rd;
    }
    free(buf);
    close(fd);
    httpd_resp_send_chunk(req, NULL, 0);
    return ESP_OK;
}

/* ── EXIF view helpers (shared by /view, /photo/exif, /last.json) ─────── */

/* Parse ?d=<bucket>&f=<leaf>, validate both (no '/', no ".." — same gate as
 * /photo), and build the on-card path. On bad input sends a 400 and returns
 * false. dparam defaults to the legacy root bucket. */
static bool photo_param_path(httpd_req_t *req, char *dparam, size_t dcap,
                             char *fname, size_t fcap, char *path, size_t pathcap) {
    snprintf(dparam, dcap, "%s", SD_LAYOUT_ROOT);
    char qbuf[128];
    if (httpd_req_get_url_query_str(req, qbuf, sizeof(qbuf)) != ESP_OK ||
        httpd_query_key_value(qbuf, "f", fname, fcap) != ESP_OK) {
        httpd_resp_send_err(req, HTTPD_400_BAD_REQUEST, "missing ?f=");
        return false;
    }
    char v[16];
    if (httpd_query_key_value(qbuf, "d", v, sizeof(v)) == ESP_OK) {
        if (!sd_layout_valid_day_param(v)) {
            httpd_resp_send_err(req, HTTPD_400_BAD_REQUEST, "bad ?d=");
            return false;
        }
        snprintf(dparam, dcap, "%s", v);
    }
    if (!sd_layout_valid_leaf(fname)) {
        httpd_resp_send_err(req, HTTPD_400_BAD_REQUEST, "filename: alphanumerics + . _ - only");
        return false;
    }
    if (strcmp(dparam, SD_LAYOUT_ROOT) == 0)
        snprintf(path, pathcap, "%s/%s", SD_MOUNT_POINT, fname);
    else
        snprintf(path, pathcap, "%s/%s/%s", SD_MOUNT_POINT, dparam, fname);
    return true;
}

/* Read the EXIF metadata out of a stored photo by peeking only the first
 * EXIF_PEEK_BYTES of the file (the APP1 segment lives right after SOI). */
static bool exif_read_file(const char *path, exif_meta_t *out) {
    if (out) memset(out, 0, sizeof(*out));
    int fd = open(path, O_RDONLY);
    if (fd < 0) return false;
    uint8_t *hdr = (uint8_t *)scratch_alloc(EXIF_PEEK_BYTES);
    bool ok = false;
    if (hdr) {
        size_t total = 0;
        while (total < EXIF_PEEK_BYTES) {
            ssize_t r = read(fd, hdr + total, EXIF_PEEK_BYTES - total);
            if (r < 0) { if (errno == EINTR) continue; break; }
            if (r == 0) break;
            total += (size_t)r;
        }
        if (total > 0) ok = exif_read(hdr, total, out);
        free(hdr);
    }
    close(fd);
    return ok;
}

/* Emit EXIF as JSON. The UserComment payload is already a JSON object, so it's
 * embedded verbatim under "telemetry" when it looks well-formed (firmware
 * always writes it so), else null. String fields are JSON-escaped. */
static void exif_send_json(httpd_req_t *req, const exif_meta_t *m, bool have) {
    httpd_resp_set_type(req, "application/json; charset=utf-8");
    if (!have) { httpd_resp_sendstr(req, "{\"exif\":false}"); return; }
    char buf[256], e[160];
    httpd_resp_sendstr_chunk(req, "{\"exif\":true");
#define J(key, val) do {                                            \
        json_escape_str((val), e, sizeof(e));                       \
        snprintf(buf, sizeof(buf), ",\"" key "\":\"%s\"", e);       \
        httpd_resp_sendstr_chunk(req, buf);                         \
    } while (0)
    J("datetime", m->datetime);
    J("offset",   m->offset);
    J("trigger",  m->trigger);
    J("model",    m->model);
    J("software", m->software);
    J("lens",     m->lens);
#undef J
    snprintf(buf, sizeof(buf), ",\"have_dt\":%s,\"telemetry\":",
             m->have_dt ? "true" : "false");
    httpd_resp_sendstr_chunk(req, buf);
    size_t ul = strlen(m->user_json);
    bool obj_ok = ul >= 2 && m->user_json[0] == '{' && m->user_json[ul - 1] == '}';
    httpd_resp_sendstr_chunk(req, obj_ok ? m->user_json : "null");
    httpd_resp_sendstr_chunk(req, "}");
    httpd_resp_sendstr_chunk(req, NULL);
}

/* GET /photo/exif?d=&f= — EXIF metadata of one stored photo as JSON. */
static esp_err_t photo_exif_get(httpd_req_t *req) {
    HTTP_AUTH_OR_RETURN(req);
    char dparam[16], fname[80], path[180];
    if (!photo_param_path(req, dparam, sizeof(dparam), fname, sizeof(fname),
                          path, sizeof(path)))
        return ESP_OK;  /* 400 already sent */
    exif_meta_t m;
    bool have = exif_read_file(path, &m);
    exif_send_json(req, &m, have);
    return ESP_OK;
}

/* GET /last.json — EXIF of the last *stored* frame (the one /last.jpg serves),
 * for live debugging without opening the gallery. */
static esp_err_t last_json_get(httpd_req_t *req) {
    HTTP_AUTH_OR_RETURN(req);
    exif_meta_t m;
    memset(&m, 0, sizeof(m));
    bool have = false;
    uint8_t *hdr = (uint8_t *)scratch_alloc(EXIF_PEEK_BYTES);
    if (hdr) {
        size_t n = camera_last_jpeg_peek_header(hdr, EXIF_PEEK_BYTES);
        if (n) have = exif_read(hdr, n, &m);
        free(hdr);
    }
    exif_send_json(req, &m, have);
    return ESP_OK;
}

/* GET /view?d=&f= — single-photo viewer: the image with a capture-time +
 * telemetry caption overlaid (HTML/CSS, no pixel burn-in), plus a full EXIF
 * table below and a link to download the original. */
static esp_err_t view_get(httpd_req_t *req) {
    HTTP_AUTH_OR_RETURN(req);
    char dparam[16], fname[80], path[180];
    if (!photo_param_path(req, dparam, sizeof(dparam), fname, sizeof(fname),
                          path, sizeof(path)))
        return ESP_OK;  /* 400 already sent */

    httpd_resp_set_type(req, "text/html; charset=utf-8");
    char buf[700], esc_f[160], esc_d[24];
    scan_html_escape(fname, esc_f, sizeof(esc_f));
    scan_html_escape(dparam, esc_d, sizeof(esc_d));

    httpd_resp_sendstr_chunk(req,
        "<!doctype html><html><head><meta charset=\"utf-8\">"
        "<meta name=\"viewport\" content=\"width=device-width,initial-scale=1\">"
        "<meta name=\"color-scheme\" content=\"dark\">"
        "<link rel=\"stylesheet\" href=\"/style.css\">");
    snprintf(buf, sizeof(buf), "<title>%s — %s</title></head><body>",
             tr(STR_VIEW_TITLE), esc_f);
    httpd_resp_sendstr_chunk(req, buf);
    send_security_banner(req);
    snprintf(buf, sizeof(buf),
        "<h1>%s <small>%s</small></h1>"
        "<p><a href=\"/photos\">%s</a> &middot; <a href=\"/\">%s</a></p>",
        tr(STR_VIEW_TITLE), esc_f, tr(STR_PH_ALL_DAYS), tr(STR_NAV_HOME));
    httpd_resp_sendstr_chunk(req, buf);

    exif_meta_t m;
    bool have = exif_read_file(path, &m);

    snprintf(buf, sizeof(buf),
        "<div class=\"frame\"><img alt=\"\" src=\"/photo?d=%s&amp;f=%s\">",
        esc_d, esc_f);
    httpd_resp_sendstr_chunk(req, buf);
    if (have) {
        char capt[256];
        exif_caption_html(&m, capt, sizeof(capt));
        if (capt[0]) {
            snprintf(buf, sizeof(buf), "<div class=\"cap\">%s</div>", capt);
            httpd_resp_sendstr_chunk(req, buf);
        }
    }
    httpd_resp_sendstr_chunk(req, "</div>");

    snprintf(buf, sizeof(buf),
        "<p><a href=\"/photo?d=%s&amp;f=%s\">&#11015; %s</a></p><h2>%s</h2>",
        esc_d, esc_f, tr(STR_DL_ORIGINAL), tr(STR_EXIF_META));
    httpd_resp_sendstr_chunk(req, buf);

    if (!have) {
        snprintf(buf, sizeof(buf), "<p class=\"empty\">%s</p></body></html>",
                 tr(STR_NO_EXIF));
        httpd_resp_sendstr_chunk(req, buf);
        httpd_resp_sendstr_chunk(req, NULL);
        return ESP_OK;
    }

    httpd_resp_sendstr_chunk(req, "<table>");
#define ROW(label, valhtml) do {                                              \
        snprintf(buf, sizeof(buf),                                            \
                 "<tr><td class=\"k\">%s</td><td class=\"v\">%s</td></tr>",    \
                 (label), (valhtml));                                         \
        httpd_resp_sendstr_chunk(req, buf);                                   \
    } while (0)
    char e[160];
    {   /* Captured = datetime (+ offset). EXIF tag names stay English. */
        char dt[24], ev[64];
        if (m.have_dt) exif_reformat_dt(m.datetime, dt, sizeof(dt));
        else           snprintf(dt, sizeof(dt), "%s", tr(STR_NO_CLOCK));
        if (m.offset[0]) snprintf(ev, sizeof(ev), "%s %.7s", dt, m.offset);
        else             snprintf(ev, sizeof(ev), "%s", dt);
        ROW("Captured", ev);
    }
    if (m.trigger[0])  { scan_html_escape(m.trigger,  e, sizeof(e)); ROW("Trigger",  e); }
    if (m.model[0])    { scan_html_escape(m.model,    e, sizeof(e)); ROW("Device",   e); }
    if (m.software[0]) { scan_html_escape(m.software, e, sizeof(e)); ROW("Firmware", e); }
    if (m.lens[0])     { scan_html_escape(m.lens,     e, sizeof(e)); ROW("Sensor",   e); }

    /* Telemetry from the UserComment JSON. prec<0 = boolean (yes/no). */
    static const struct { const char *key, *label, *unit; int prec; } TEL[] = {
        {"agc", "AGC", "", 0}, {"ir", "IR", "", -1},
        {"rssi", "RSSI", "&nbsp;dBm", 0}, {"framesize", "Framesize", "", 0},
        {"quality", "JPEG&nbsp;quality", "", 0},
        {"mcu_c", "MCU&nbsp;temp", "&nbsp;&deg;C", 1},
        {"vbatt", "Battery", "&nbsp;V", 3}, {"soc", "SOC", "&nbsp;%", 0},
        {"heap", "Free&nbsp;heap", "&nbsp;B", 0}, {"uptime_s", "Uptime", "&nbsp;s", 0},
        {"capture_ms", "Capture", "&nbsp;ms", 0}, {"seq", "Sequence", "", 0},
    };
    for (size_t i = 0; i < sizeof(TEL) / sizeof(TEL[0]); i++) {
        double v;
        if (!exif_json_num(m.user_json, TEL[i].key, &v)) continue;
        char vv[48];
        if (TEL[i].prec < 0)
            snprintf(vv, sizeof(vv), "%s", (v != 0) ? "yes" : "no");
        else
            snprintf(vv, sizeof(vv), "%.*f%s", TEL[i].prec, v, TEL[i].unit);
        ROW(TEL[i].label, vv);
    }
#undef ROW
    httpd_resp_sendstr_chunk(req, "</table></body></html>");
    httpd_resp_sendstr_chunk(req, NULL);
    return ESP_OK;
}

/* GET /i2c — sweep the shared I²C bus and report which addresses answer,
 * annotated against the chips we ship drivers for. Read-only — safe to
 * call from the field. Useful when wiring a new sensor: re-hit the
 * endpoint after each wire move instead of rebooting to see the boot
 * scan again. */
static esp_err_t i2c_scan_get(httpd_req_t *req) {
    HTTP_AUTH_OR_RETURN(req);  /* parity with the other sensitive endpoints */
    char report[1024];
    i2c_bus_scan_report(report, sizeof(report));
    httpd_resp_set_type(req, "text/plain; charset=utf-8");
    return httpd_resp_send(req, report, strlen(report));
}

/* GET /i2c/bus1_diag — deep diagnostic for the bit-banged bus1 (D6/D7).
 *
 * Reports — in this order:
 *   pins         which GPIOs the bit-bang has cached (-1 = uninitialised)
 *   idle_pre     SDA/SCL pad levels right now, before we touch anything
 *   reinit_rc    return code of forcing a fresh i2c_bb init (recovery
 *                clock burst included). Even on a "working" bus we run
 *                this because we want the idle reading *after* the
 *                recovery sequence too — that's what catches a slave
 *                that wedged a few seconds after boot.
 *   idle_post    SDA/SCL pad levels after reinit
 *   probe_0x44   number of ACKs out of 8 probes at SHT41 address
 *   probe_0x36   number of ACKs out of 8 probes at MAX17048 address
 *
 * Reading: idle_post must be (1,1) for the bus to be electrically usable.
 * If either is 0 → line stuck low (slave holding it, wrong pin, missing
 * pull-up, or a peripheral grabbed the IO_MUX pad after our init). With
 * idle (1,1) and probe_0x44=0 the slave isn't responding at the expected
 * address — usually means it's wired to a different addr-strap or its
 * VDD isn't connected. */
static esp_err_t i2c_bus1_diag_get(httpd_req_t *req) {
    HTTP_AUTH_OR_RETURN(req);  /* parity with the other sensitive endpoints */
    char body[768];
    char *p = body;
    size_t left = sizeof(body);

    int sda_pin = -1, scl_pin = -1;
    i2c_bb_pins(&sda_pin, &scl_pin);

    int sda_pre = -1, scl_pre = -1;
    i2c_bb_idle_read(&sda_pre, &scl_pre);
    /* Reflect the live pin-map view of which GPIOs bus1 SHOULD be on
     * (vs sda_pin/scl_pin = what i2c_bb_init actually cached). After
     * the migration to the pin function map these can disagree only
     * if NVS was modified between the bus1_ensure call at boot and
     * now — e.g. operator reassigned slots via MQTT without rebooting
     * yet. */
    int sda_cfg = app_config_pin_for_first("i2c1_sda");
    int scl_cfg = app_config_pin_for_first("i2c1_scl");
    int n = snprintf(p, left,
                     "pins: sda=GPIO%d scl=GPIO%d (pin_map %d/%d)\n"
                     "idle_pre:  SDA=%d SCL=%d\n",
                     sda_pin, scl_pin, sda_cfg, scl_cfg,
                     sda_pre, scl_pre);
    if (n > 0 && (size_t)n < left) { p += n; left -= n; }

    esp_err_t e = (sda_cfg >= 0 && scl_cfg >= 0)
        ? i2c_bb_reinit(sda_cfg, scl_cfg)
        : ESP_ERR_INVALID_STATE;
    int sda_post = -1, scl_post = -1;
    i2c_bb_idle_read(&sda_post, &scl_post);
    n = snprintf(p, left,
                 "reinit_rc: %s\nidle_post: SDA=%d SCL=%d\n",
                 esp_err_to_name(e), sda_post, scl_post);
    if (n > 0 && (size_t)n < left) { p += n; left -= n; }

    /* Drive-low readback. Healthy IO buffer reads 0 when we sink the
     * line. A pad whose output stage died (ESD, latch-up) stays at 1
     * because only the internal pull-up is active. This separates a
     * "no slave wired" symptom from a "XIAO can't drive bus1 anymore"
     * symptom — both produce the same probe=0/8 reading. */
    int sda_dl = -1, scl_dl = -1;
    i2c_bb_drive_low_check(&sda_dl, &scl_dl);
    n = snprintf(p, left,
                 "drive_low_readback: SDA=%d SCL=%d  (expect 0/0 on a healthy pad)\n",
                 sda_dl, scl_dl);
    if (n > 0 && (size_t)n < left) { p += n; left -= n; }

    int sda_to_scl = -1, scl_to_sda = -1;
    i2c_bb_short_check(&sda_to_scl, &scl_to_sda);
    n = snprintf(p, left,
                 "short_check: sda→scl_bleed=%d scl→sda_bleed=%d  "
                 "(both 0 = clean; either 1 = SDA/SCL shorted)\n",
                 sda_to_scl, scl_to_sda);
    if (n > 0 && (size_t)n < left) { p += n; left -= n; }

    /* Drive-low leaves the bit-bang state pristine (both lines released
     * back to HIGH at the end), but a slave that saw the spurious SDA
     * falling edge during the check may be sitting in addressing limbo.
     * One more reinit (recovery clocks + STOP) clears that. */
    if (sda_cfg >= 0 && scl_cfg >= 0) {
        i2c_bb_reinit(sda_cfg, scl_cfg);
    }

    /* Wider scan: list every 7-bit address that ACKs on bus1. Same
     * single-shot we do in /i2c, but here we always print so the
     * operator can spot a strap-variant slave at 0x45/0x46/0x47 (SHT4x)
     * or 0x6C (MAX17041/44) without re-hitting /i2c afterward. */
    int n_found = 0;
    n = snprintf(p, left, "scan: ");
    if (n > 0 && (size_t)n < left) { p += n; left -= n; }
    for (uint8_t a = 0x08; a <= 0x77; a++) {
        if (i2c_bb_probe(a)) {
            n = snprintf(p, left, "%s0x%02x", n_found ? " " : "", a);
            if (n > 0 && (size_t)n < left) { p += n; left -= n; }
            n_found++;
        }
    }
    if (!n_found) {
        n = snprintf(p, left, "(none)");
        if (n > 0 && (size_t)n < left) { p += n; left -= n; }
    }
    n = snprintf(p, left, "\n");
    if (n > 0 && (size_t)n < left) { p += n; left -= n; }

    int ack44 = 0, ack36 = 0;
    for (int i = 0; i < 8; i++) {
        if (i2c_bb_probe(0x44))
            ack44++;
        if (i2c_bb_probe(0x36))
            ack36++;
    }
    n = snprintf(p, left,
                 "probe_0x44 (SHT41): %d/8\n"
                 "probe_0x36 (MAX17048): %d/8\n",
                 ack44, ack36);
    if (n > 0 && (size_t)n < left) { p += n; left -= n; }

    /* Active recovery hook: if probes ACKed but the bus1 SHT41 (registry id
     * "sht1") is still not ready (sensor was just plugged in / wires fixed
     * and the periodic re-probe hasn't fired yet), force a probe directly
     * from this handler. Means the operator hits /i2c/bus1_diag once, sees
     * ACKs, AND the homepage's "outside" row goes live without a reboot. */
    if (ack44 >= 4 && !cb_sensor_ready("sht1")) {
        esp_err_t ie = cb_sensor_probe("sht1");
        n = snprintf(p, left,
                     "sht1 probe triggered (probes ACKed): %s — now ready=%d\n",
                     esp_err_to_name(ie), (int)cb_sensor_ready("sht1"));
        if (n > 0 && (size_t)n < left) { p += n; left -= n; }
    } else {
        n = snprintf(p, left, "sht1 ready: %d  (cached state)\n",
                     (int)cb_sensor_ready("sht1"));
        if (n > 0 && (size_t)n < left) { p += n; left -= n; }
    }

    /* SDA/SCL swap test — flip the firmware pin assignment and re-probe.
     * If the breakout / harness has SDA-SCL crossed (common when both
     * lines are red/yellow and the silkscreen got misread), this pass
     * will ACK while the default pass won't. Restore the canonical pin
     * order at the end so subsequent /i2c calls and the periodic
     * sht41_ext re-probe see the bus as expected. */
    int swap_ack44 = 0;
    if (sda_cfg >= 0 && scl_cfg >= 0 &&
        i2c_bb_reinit(scl_cfg, sda_cfg) == ESP_OK) {
        for (int i = 0; i < 8; i++) {
            if (i2c_bb_probe(0x44))
                swap_ack44++;
        }
    }
    if (sda_cfg >= 0 && scl_cfg >= 0) {
        i2c_bb_reinit(sda_cfg, scl_cfg);
    }
    n = snprintf(p, left,
                 "swap_test (sda=GPIO%d scl=GPIO%d): probe_0x44 %d/8\n",
                 scl_cfg, sda_cfg, swap_ack44);
    if (n > 0 && (size_t)n < left) { p += n; left -= n; }

    httpd_resp_set_type(req, "text/plain; charset=utf-8");
    return httpd_resp_send(req, body, strlen(body));
}

/* GET /sht41/bus1 — single read from the diagnostic SHT41 on the
 * bit-banged bus1 (D6/D7). Returns "T=…°C RH=…%" plaintext, or an
 * error message with the underlying esp_err_t name on failure. No
 * caching here — this is a manual diagnostic endpoint. */
static esp_err_t sht41_bus1_get(httpd_req_t *req) {
    HTTP_AUTH_OR_RETURN(req);  /* parity with the other sensitive endpoints */
    esp_err_t e = cb_sensor_probe("sht1");   /* (re)detect a just-wired sensor */
    cb_sensor_refresh_one("sht1");           /* force a fresh read into the cache */
    float t_c = 0, rh = 0;
    char body[96];
    int n;
    if (cb_sensor_chan("sht1", "temp_ext", &t_c) &&
        cb_sensor_chan("sht1", "humidity_ext", &rh)) {
        n = snprintf(body, sizeof(body), "T=%.2f°C  RH=%.2f%%\n", t_c, rh);
    } else {
        /* No reading: nothing on bus1 (D6/D7) or a wired sensor faulted.
         * esp_err_to_name(e) carries the probe result — typically
         * ESP_ERR_NOT_FOUND when the diagnostic SHT41 simply isn't fitted. */
        n = snprintf(body, sizeof(body), "sht41 bus1: not detected (%s)\n",
                     esp_err_to_name(e));
    }
    httpd_resp_set_type(req, "text/plain; charset=utf-8");
    return httpd_resp_send(req, body, n);
}

/* GET /sensors — on-demand FRESH read of every registered I²C sensor
 * (bus0 + bus1), straight from the sensor registry. Unlike the homepage
 * (which shows the telemetry-refreshed caches), this forces a live read,
 * so it's the diagnostic to trust for "is the sensor actually reading
 * right now?" — across all sensors, not just the two bus1 ones. New
 * sensors appear here automatically. */
static esp_err_t sensors_get(httpd_req_t *req) {
    HTTP_AUTH_OR_RETURN(req);  /* parity with the other sensitive endpoints */
    cb_sensors_refresh();      /* live reads (on-demand/diagnostic, rare) */
    char body[768];
    int o = 0;
    for (size_t si = 0; si < CB_SENSORS_N && o < (int)sizeof(body) - 1; si++) {
        const cb_sensor_t *s = &CB_SENSORS[si];
        bool present = s->read_ok ? s->read_ok() : (!s->present || s->present());
        o += snprintf(body + o, sizeof(body) - o, "%-4s %-16s bus%d 0x%02x  %s\n",
                      s->id, s->name, (int)s->bus, s->addr, present ? "present" : "ABSENT");
        if (!present)
            continue;
        for (size_t ci = 0; ci < s->n_chans && o < (int)sizeof(body) - 1; ci++) {
            const cb_chan_t *c = &s->chans[ci];
            float v;
            if (c->read(&v) && isfinite(v))
                o += snprintf(body + o, sizeof(body) - o, "  %-13s = %.*f %s\n",
                              c->obj, c->decimals, (double)v, c->unit);
            else
                o += snprintf(body + o, sizeof(body) - o, "  %-13s = n/a\n", c->obj);
        }
    }
    httpd_resp_set_type(req, "text/plain; charset=utf-8");
    return httpd_resp_send(req, body, o);
}

/* Minimal in-place percent-decode (%XX + '+'→space) for a query value. */
static void url_decode(char *s) {
    char *o = s;
    for (char *i = s; *i; i++) {
        if (*i == '+') {
            *o++ = ' ';
        } else if (*i == '%' && isxdigit((unsigned char)i[1]) && isxdigit((unsigned char)i[2])) {
            char h[3] = {i[1], i[2], 0};
            *o++ = (char)strtol(h, NULL, 16);
            i += 2;
        } else {
            *o++ = *i;
        }
    }
    *o = 0;
}

/* GET /oled/qr[?text=...] — render a QR on the bench OLED for ~90 s. Default
 * text is now the board's OWN web-UI URL (https://<id>.<domain>/), so scanning
 * the panel opens the live page on a phone; pass ?text=... to override. The
 * screen returns to the status page afterwards. */
static esp_err_t oled_qr_get(httpd_req_t *req) {
    HTTP_AUTH_OR_RETURN(req);
    char text[160];
    device_url(text, sizeof(text), wifi_mgr_get_domain());
    char q[256], val[160];
    if (httpd_req_get_url_query_str(req, q, sizeof(q)) == ESP_OK &&
        httpd_query_key_value(q, "text", val, sizeof(val)) == ESP_OK) {
        url_decode(val);
        strlcpy(text, val, sizeof(text));
    }
    bool ok = oled_show_qr(text);
    char body[240];
    int n = snprintf(body, sizeof(body), "%s\n%s\n",
                     ok ? "QR shown on OLED for ~90 s — scan it." : "no OLED present", text);
    httpd_resp_set_type(req, "text/plain; charset=utf-8");
    return httpd_resp_send(req, body, n);
}

/* GET /oled/logo.bin — the EFFECTIVE boot logo (NVS custom, else baked
 * default) as raw 1024 bytes, so the upload form can show what's current. */
static esp_err_t oled_logo_bin_get(httpd_req_t *req) {
    HTTP_AUTH_OR_RETURN(req);
    uint8_t *buf = malloc(OLED_LOGO_BYTES);
    if (!buf)
        return httpd_resp_send_500(req);
    oled_get_boot_logo(buf, OLED_LOGO_BYTES);
    httpd_resp_set_type(req, "application/octet-stream");
    esp_err_t e = httpd_resp_send(req, (const char *)buf, OLED_LOGO_BYTES);
    free(buf);
    return e;
}
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
